vinmarshall/Radio-Shack-Time-Lapse/images/camera/camera_back_1.jpg

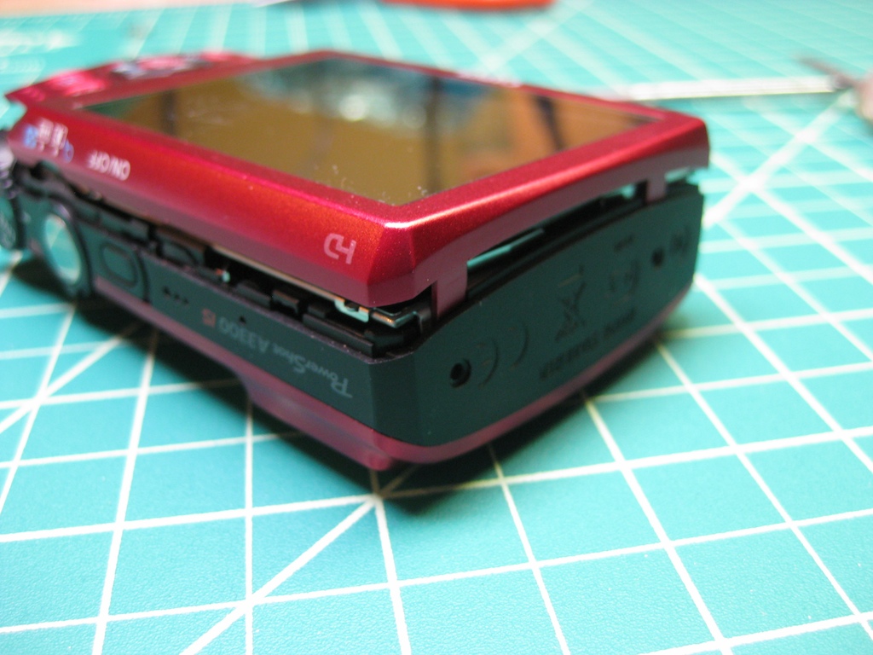
images/camera/camera_back_1.jpg
