vinmarshall/Radio-Shack-Time-Lapse/images/camera/camera_back_2.jpg

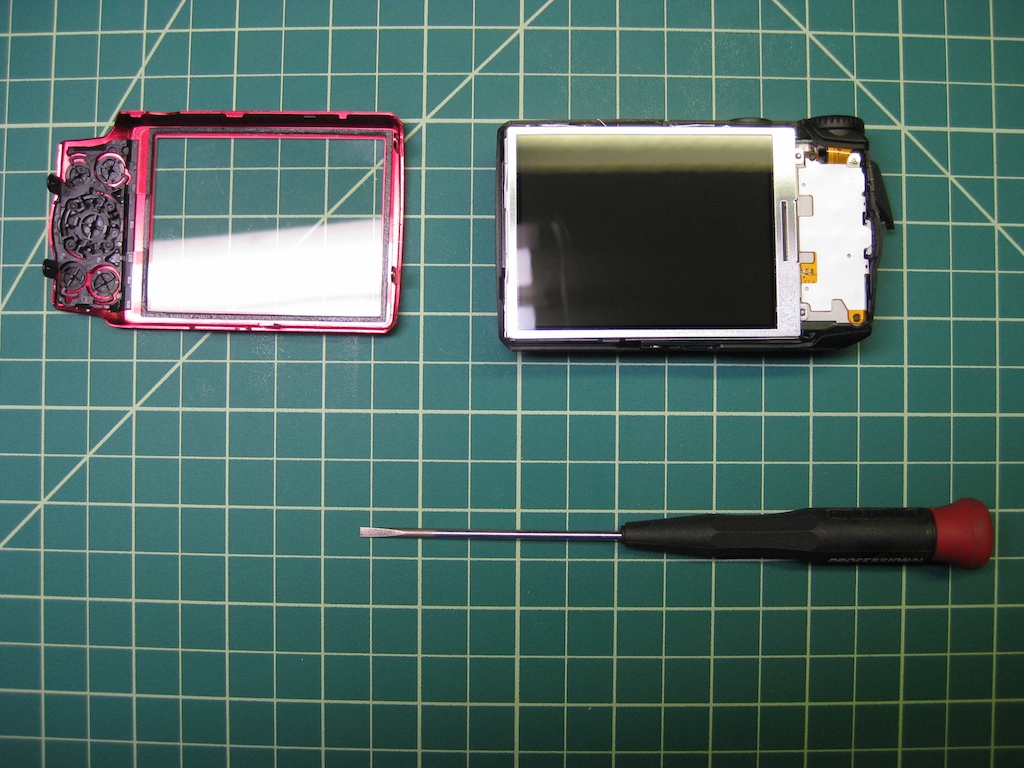
images/camera/camera_back_2.jpg
