vinmarshall/Radio-Shack-Time-Lapse/images/camera/camera_button_cover_1.jpg

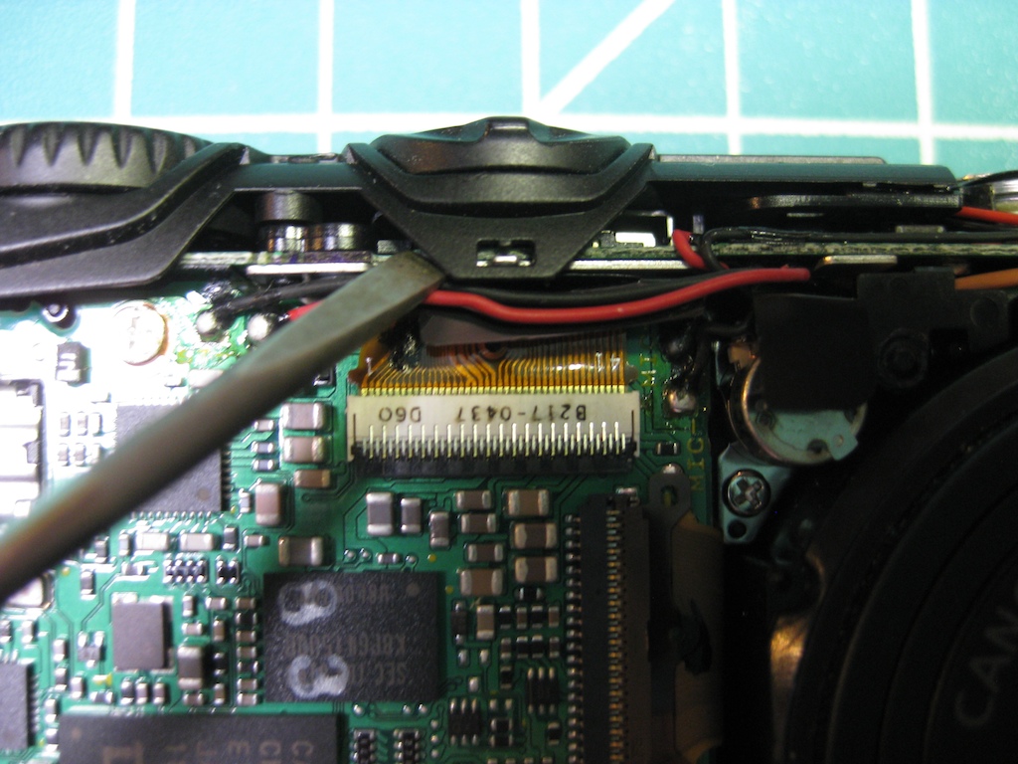
images/camera/camera_button_cover_1.jpg
