vinmarshall/Radio-Shack-Time-Lapse/images/camera/camera_button_cover_2.jpg

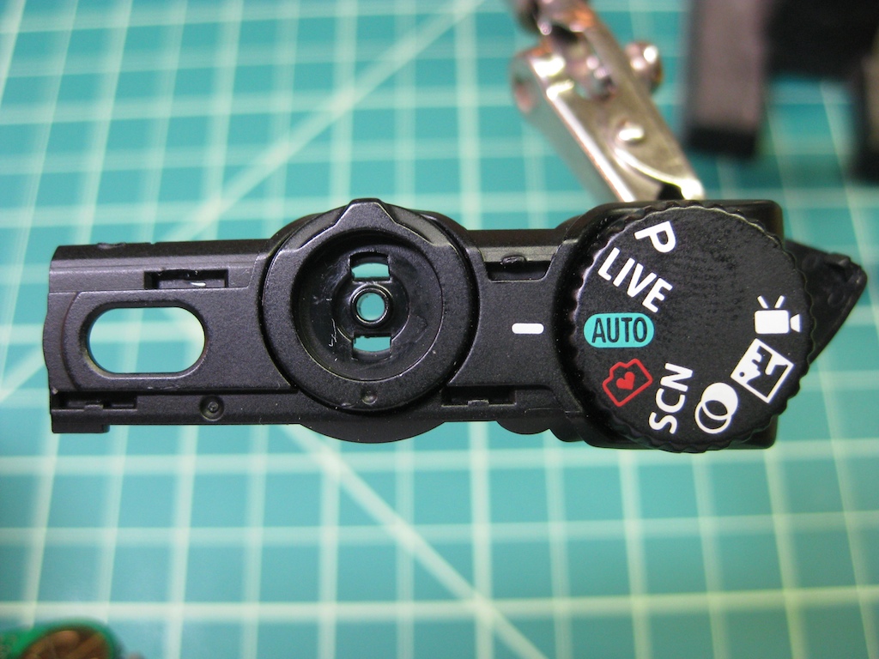
images/camera/camera_button_cover_2.jpg
