vinmarshall/Radio-Shack-Time-Lapse/images/camera/camera_button_cover_3.jpg

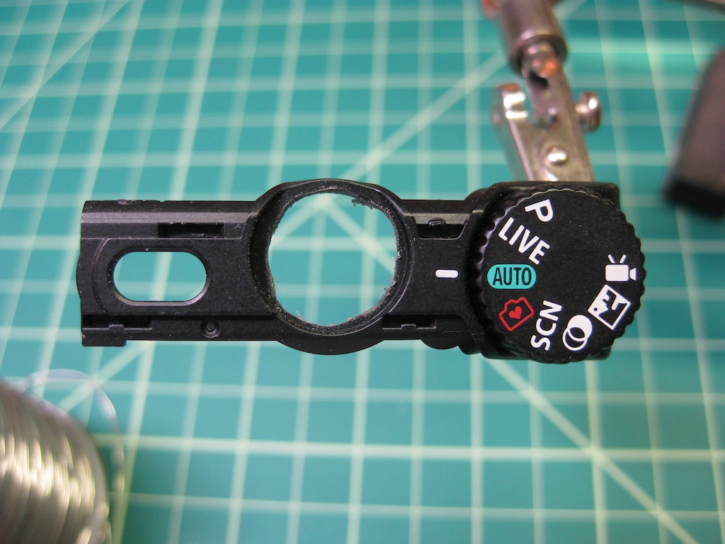
images/camera/camera_button_cover_3.jpg
