vinmarshall/Radio-Shack-Time-Lapse/images/camera/camera_front_1.jpg

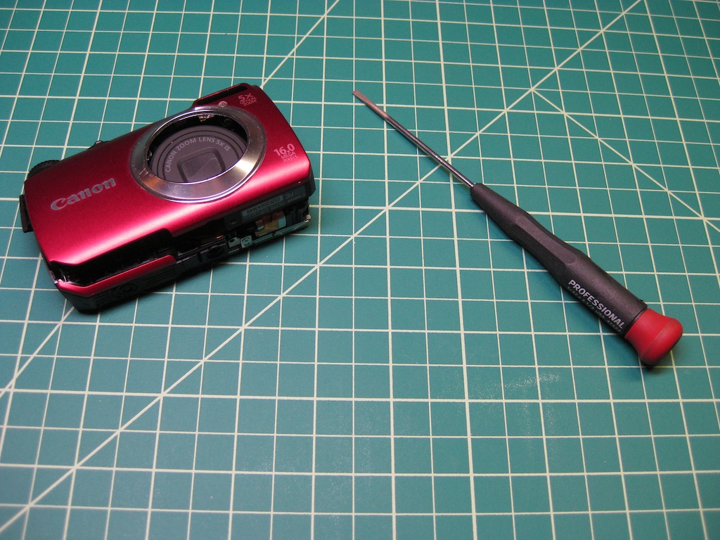
images/camera/camera_front_1.jpg
