vinmarshall/Radio-Shack-Time-Lapse/images/camera/camera_front_2.jpg

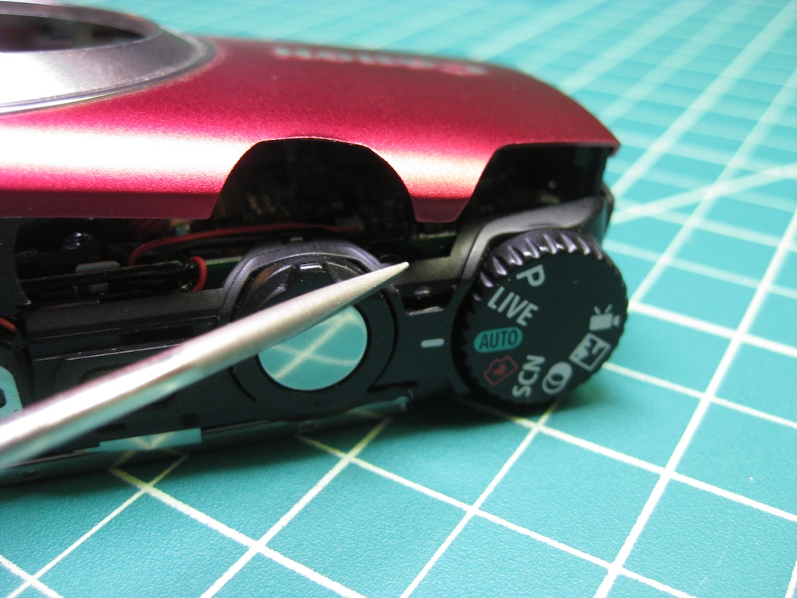
images/camera/camera_front_2.jpg
