vinmarshall/Radio-Shack-Time-Lapse/images/camera/camera_front_3.jpg

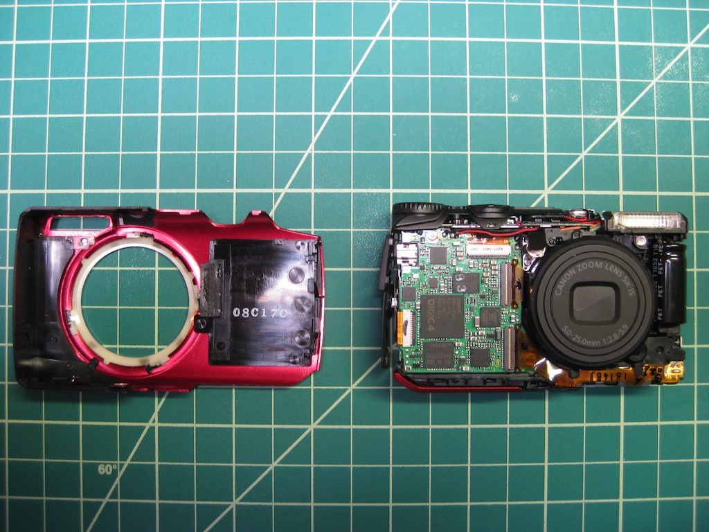
images/camera/camera_front_3.jpg
