vinmarshall/Radio-Shack-Time-Lapse/images/camera/finished.jpg

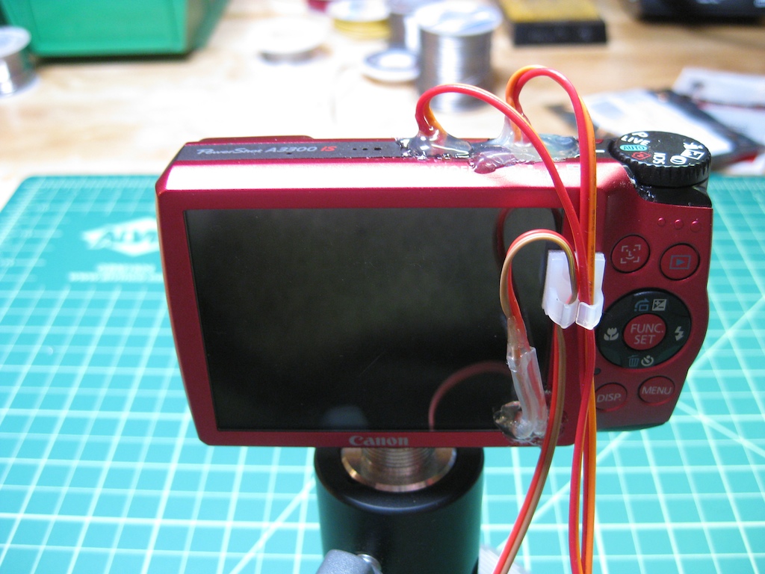
images/camera/finished.jpg
