vinmarshall/Radio-Shack-Time-Lapse/images/camera/hidden_screw.jpg

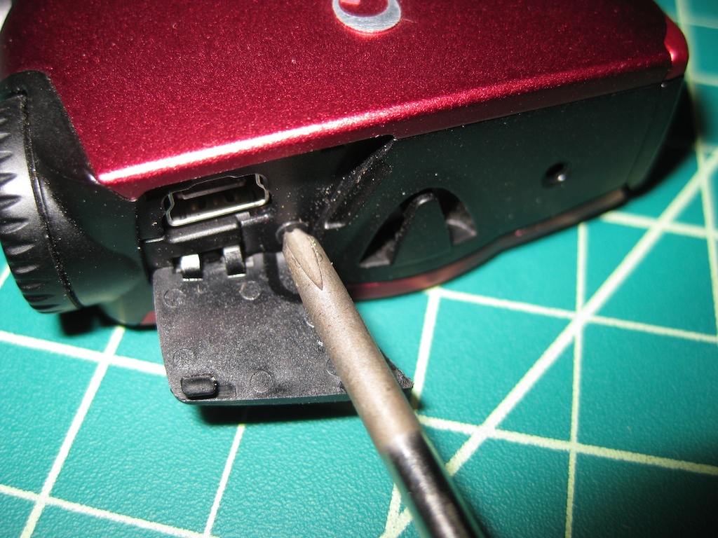
images/camera/hidden_screw.jpg
