vinmarshall/Radio-Shack-Time-Lapse/images/camera/leads_1.jpg

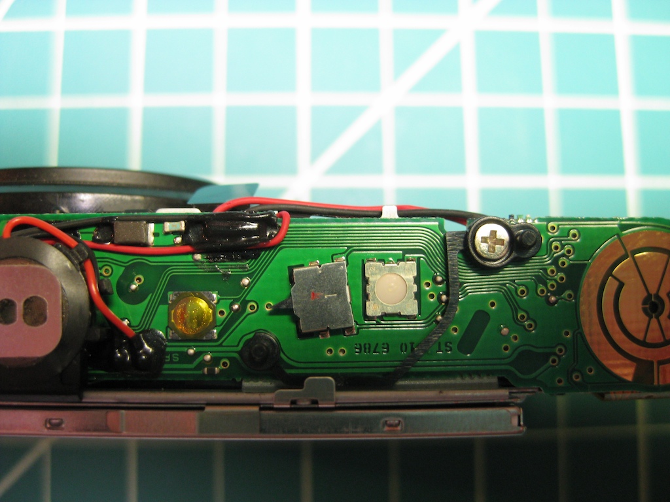
images/camera/leads_1.jpg
