vinmarshall/Radio-Shack-Time-Lapse/images/camera/leads_2.jpg

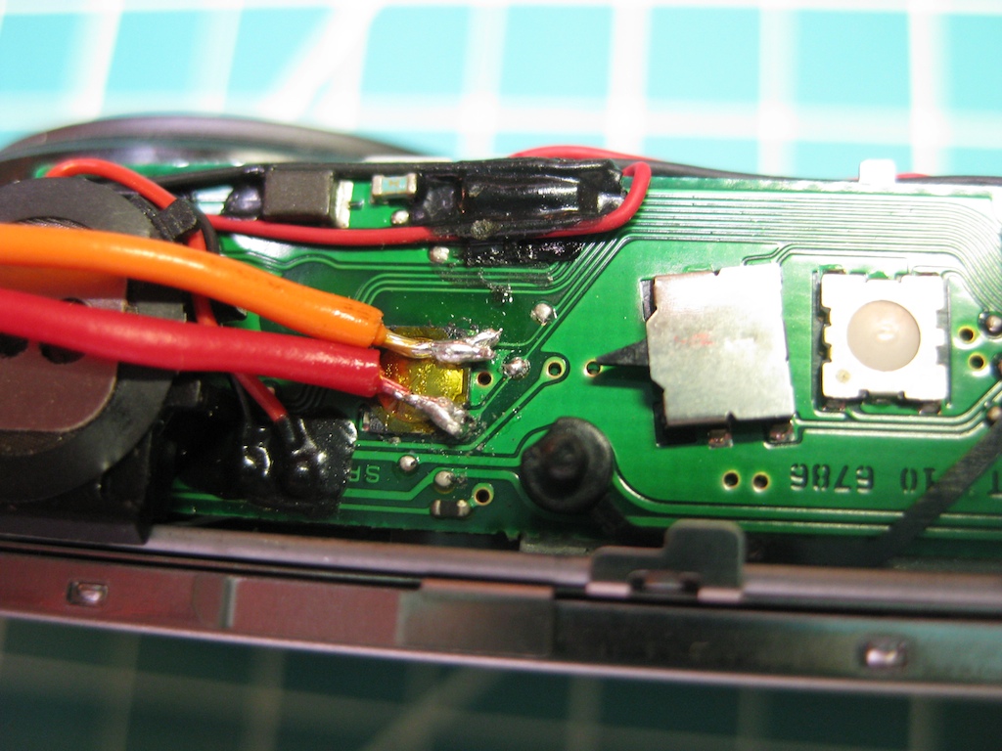
images/camera/leads_2.jpg
