vinmarshall/Radio-Shack-Time-Lapse/images/camera/leads_3.jpg

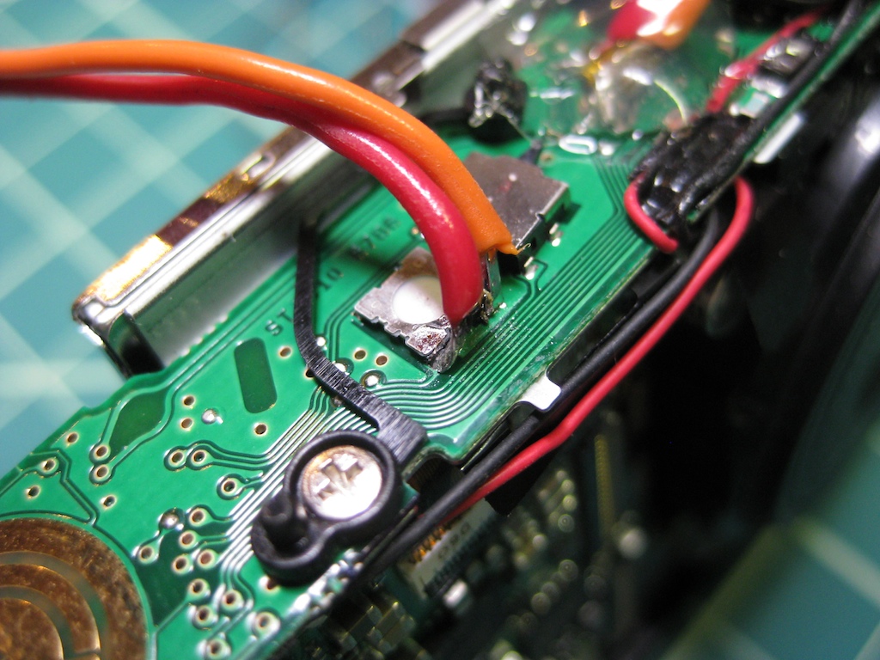
images/camera/leads_3.jpg
