vinmarshall/Radio-Shack-Time-Lapse/images/camera/leads_4.jpg

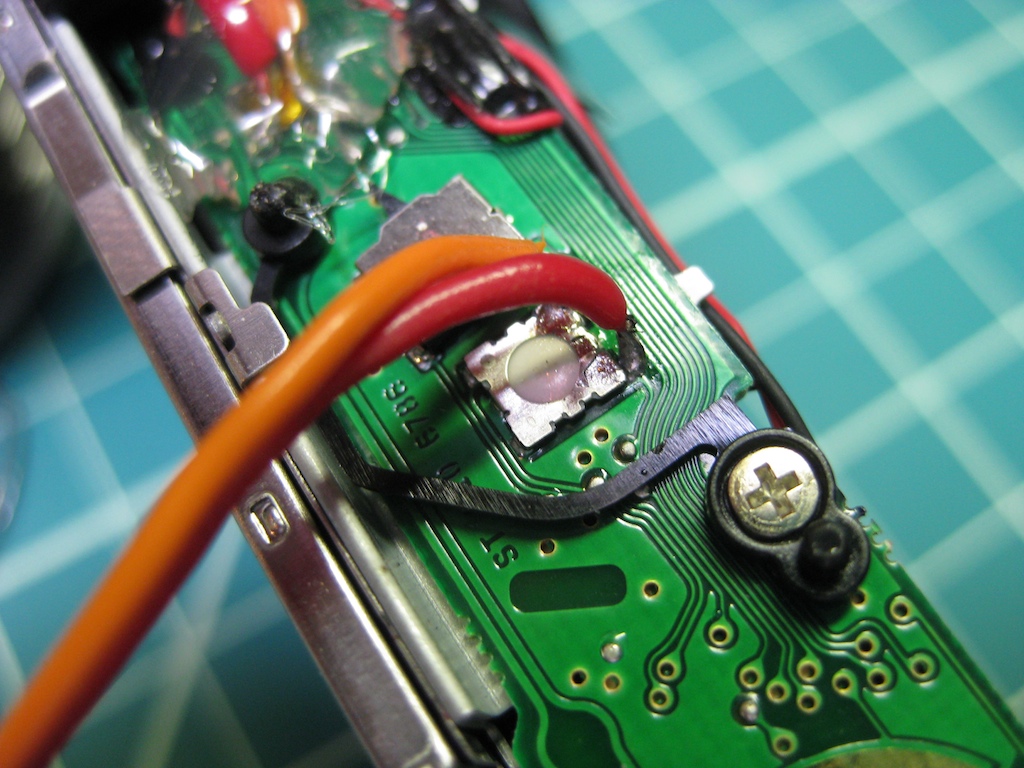
images/camera/leads_4.jpg
