vinmarshall/Radio-Shack-Time-Lapse/images/camera/leads_5.jpg

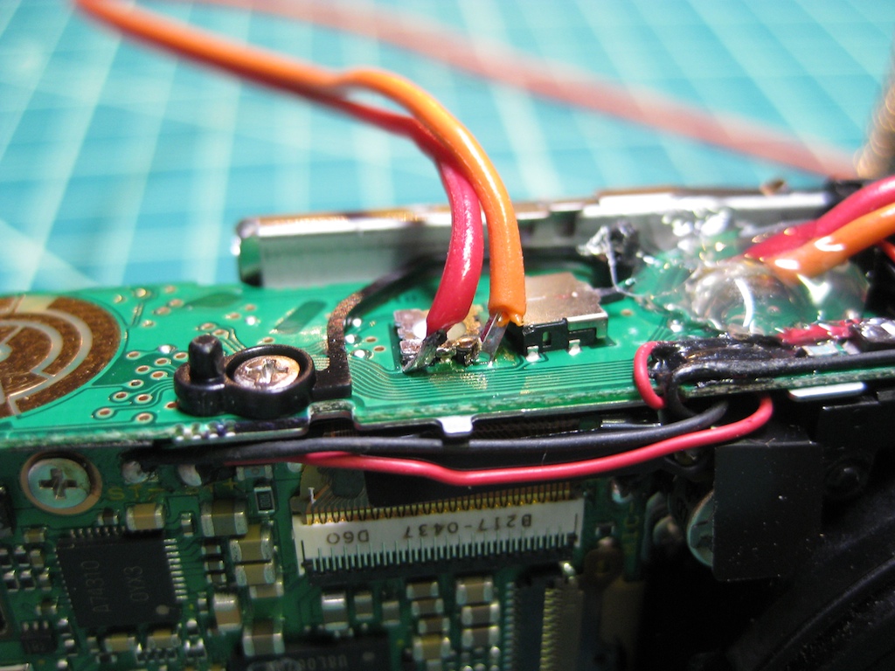
images/camera/leads_5.jpg
