vinmarshall/Radio-Shack-Time-Lapse/images/camera/leads_6.jpg

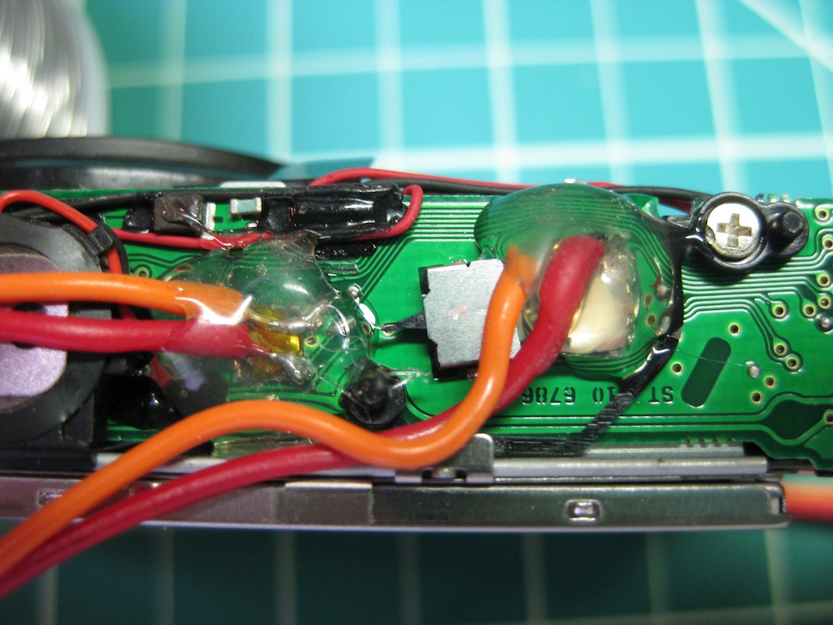
images/camera/leads_6.jpg
