vinmarshall/Radio-Shack-Time-Lapse/images/camera/leads_7.jpg

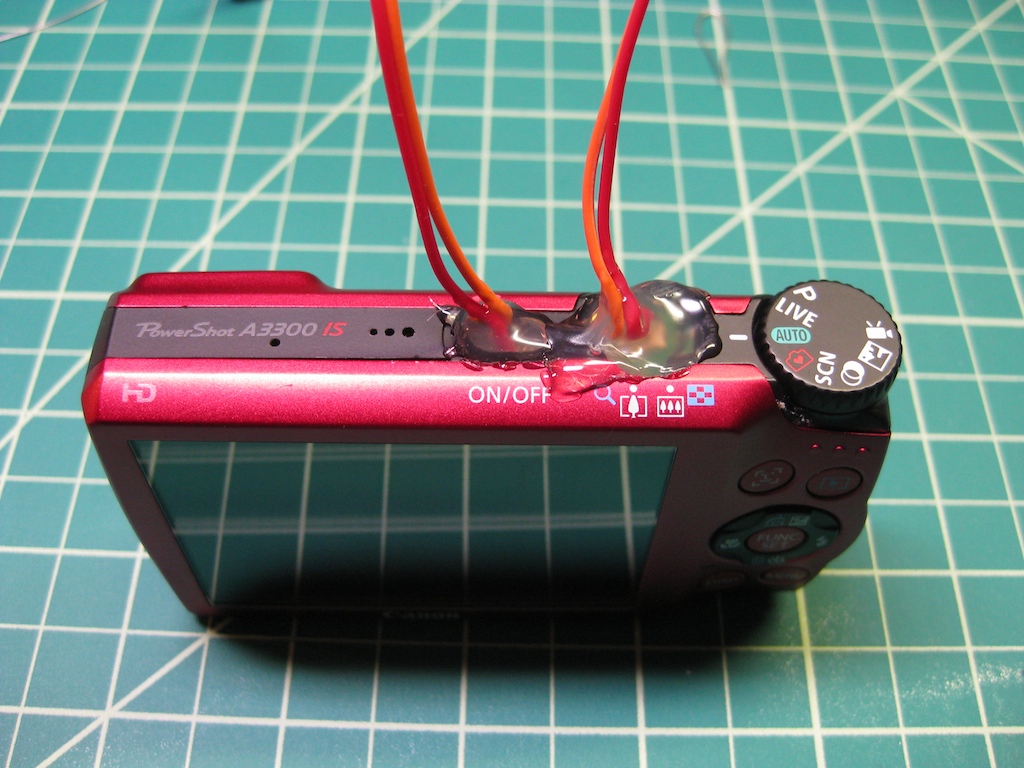
images/camera/leads_7.jpg
