vinmarshall/Radio-Shack-Time-Lapse/images/camera/leads_8.jpg

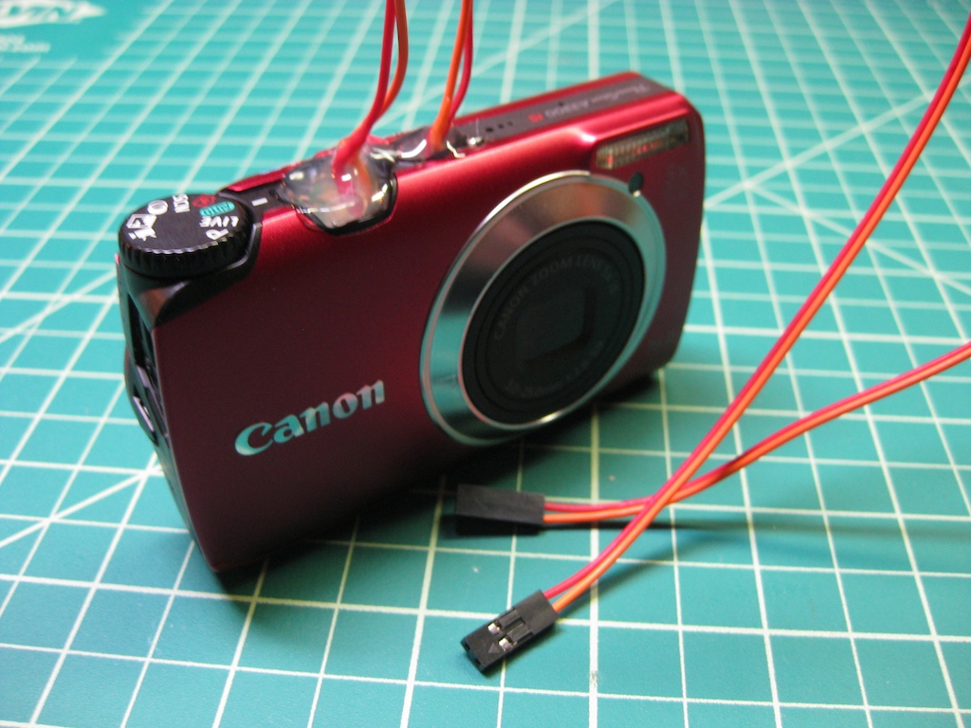
images/camera/leads_8.jpg
