vinmarshall/Radio-Shack-Time-Lapse/images/camera/photoresistor_1.jpg

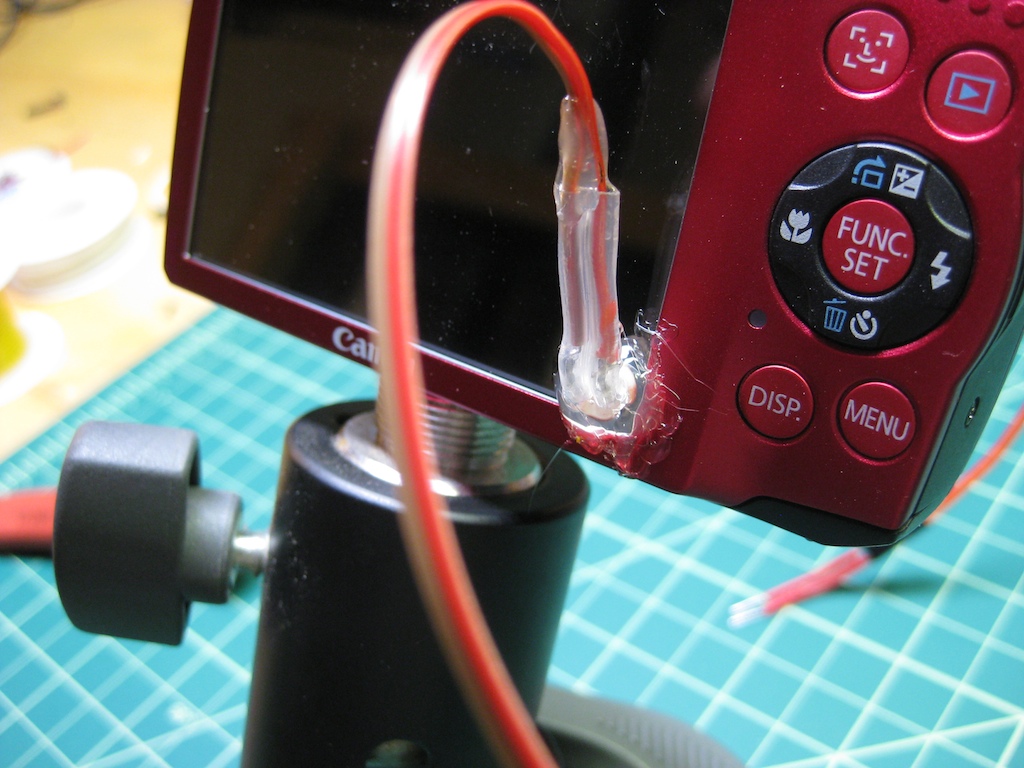
images/camera/photoresistor_1.jpg
