vinmarshall/Radio-Shack-Time-Lapse/images/camera/photoresistor_2.jpg

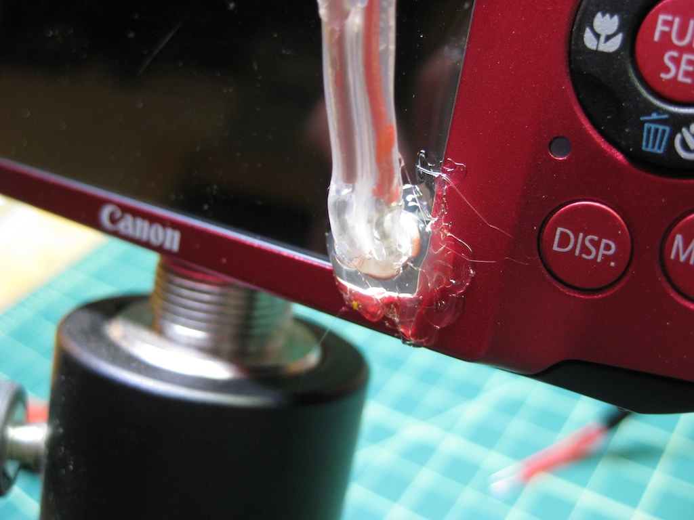
images/camera/photoresistor_2.jpg
