vinmarshall/Radio-Shack-Time-Lapse/images/camera/the_buttons.jpg

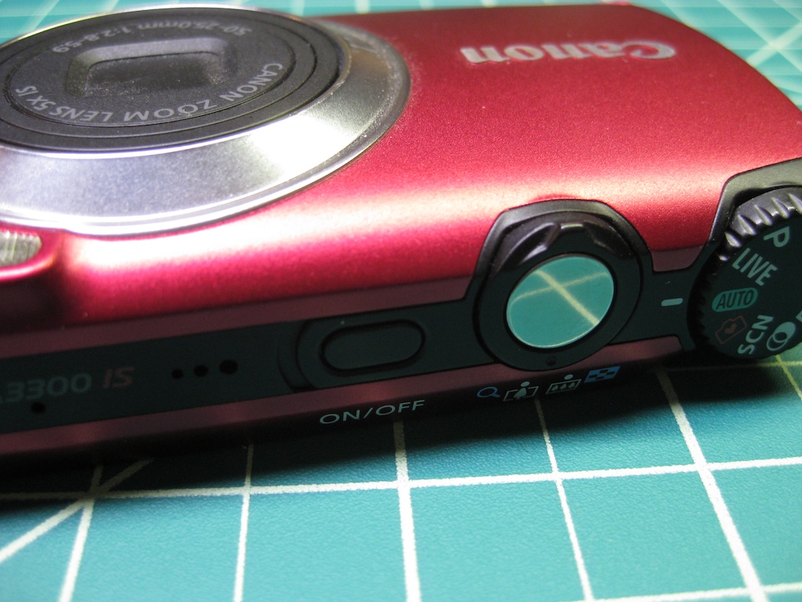
images/camera/the_buttons.jpg
