vinmarshall/Radio-Shack-Time-Lapse/images/panel/jumper.jpg

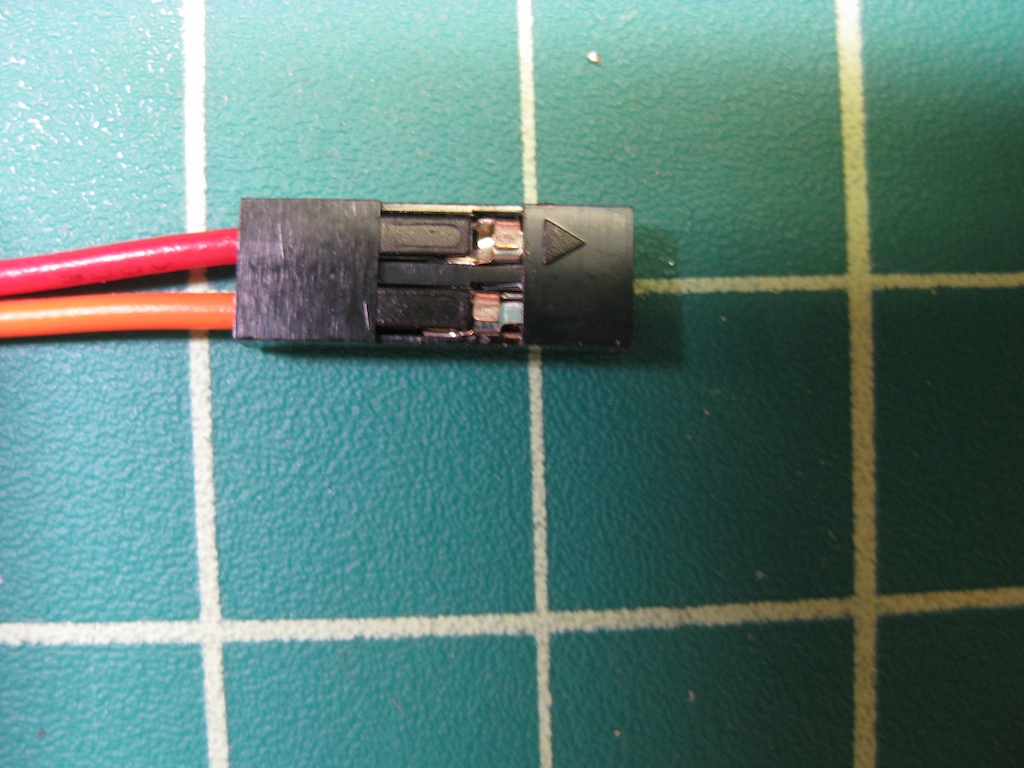
images/panel/jumper.jpg
