vinmarshall/Radio-Shack-Time-Lapse/images/panel/lamp_1.jpg

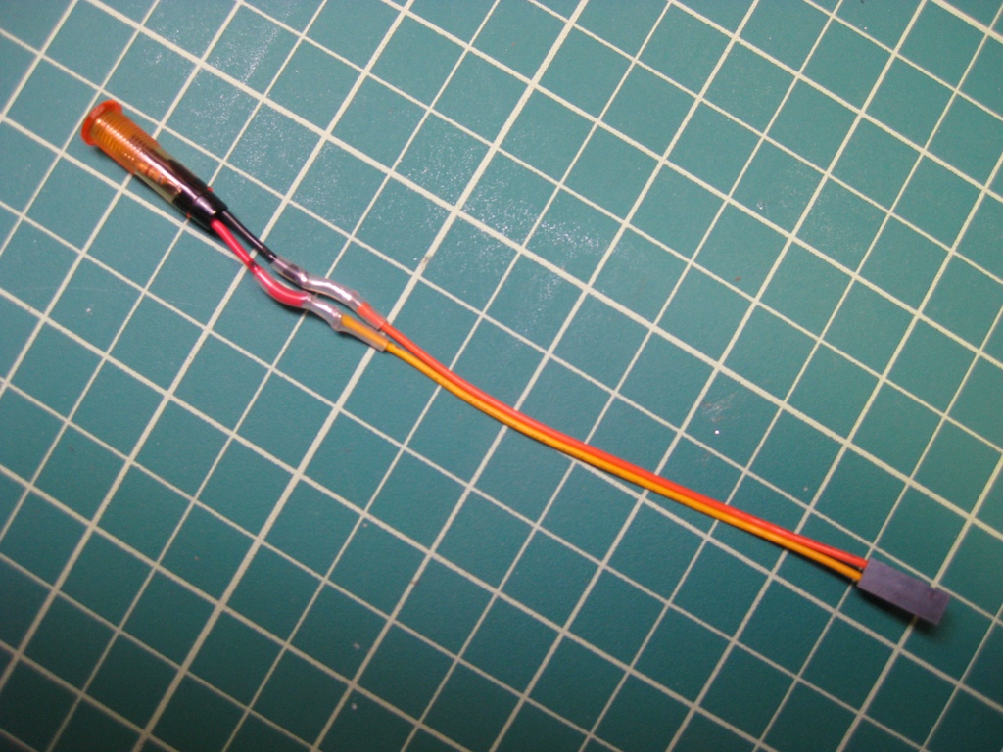
images/panel/lamp_1.jpg
