vinmarshall/Radio-Shack-Time-Lapse/images/panel/lamp_2.jpg

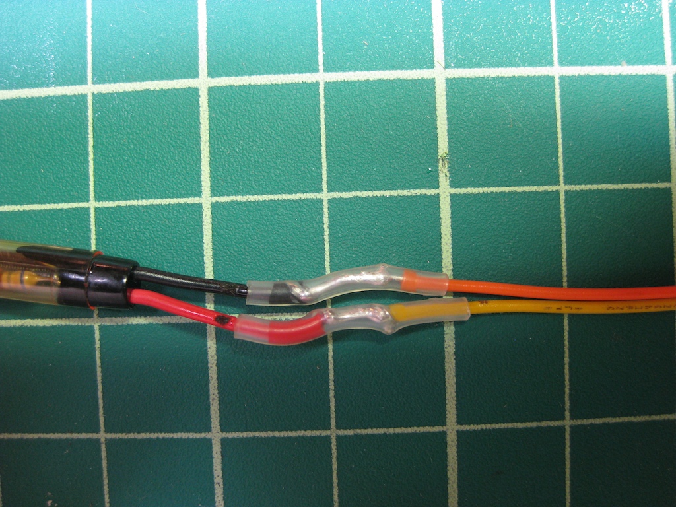
images/panel/lamp_2.jpg
