vinmarshall/Radio-Shack-Time-Lapse/images/panel/lamp_3.jpg

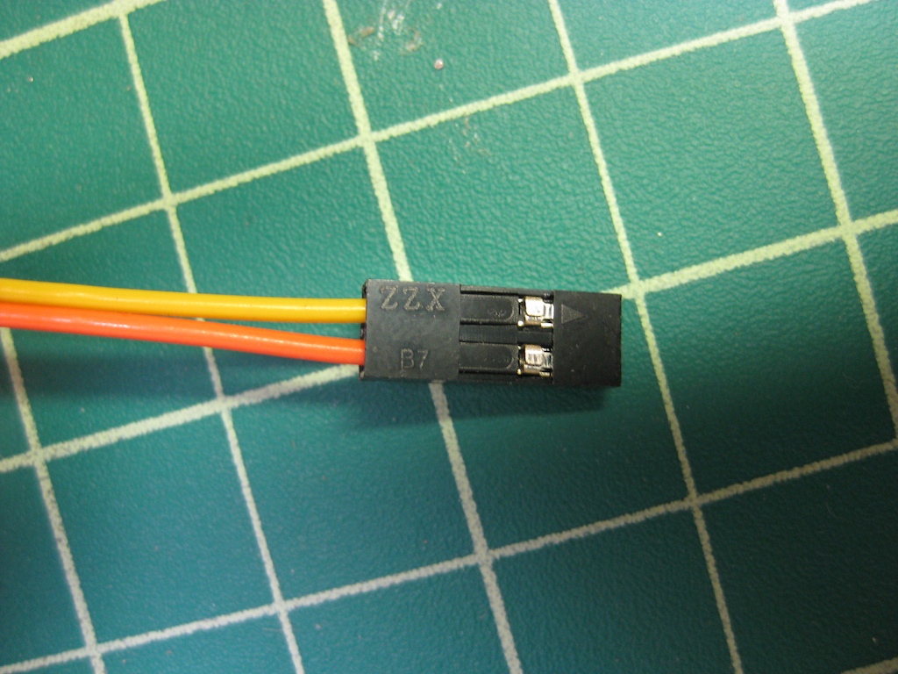
images/panel/lamp_3.jpg
