vinmarshall/Radio-Shack-Time-Lapse/images/panel/panel_back.jpg

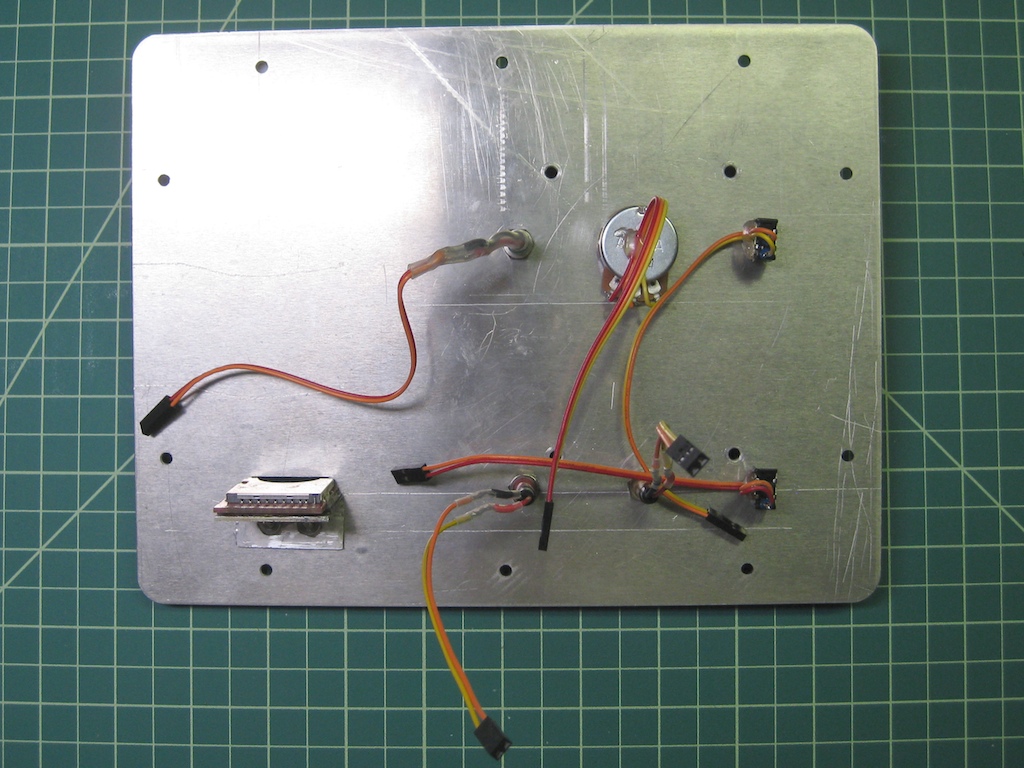
images/panel/panel_back.jpg
