vinmarshall/Radio-Shack-Time-Lapse/images/panel/panel_front.jpg

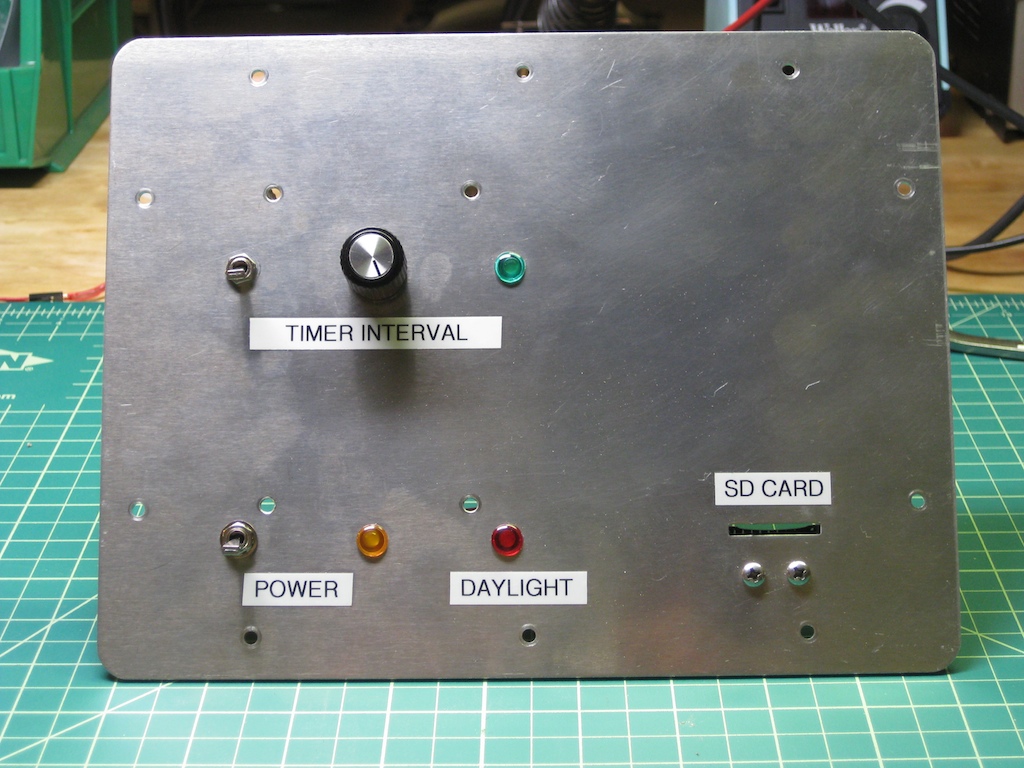
images/panel/panel_front.jpg
