vinmarshall/Radio-Shack-Time-Lapse/images/panel/pins.jpg

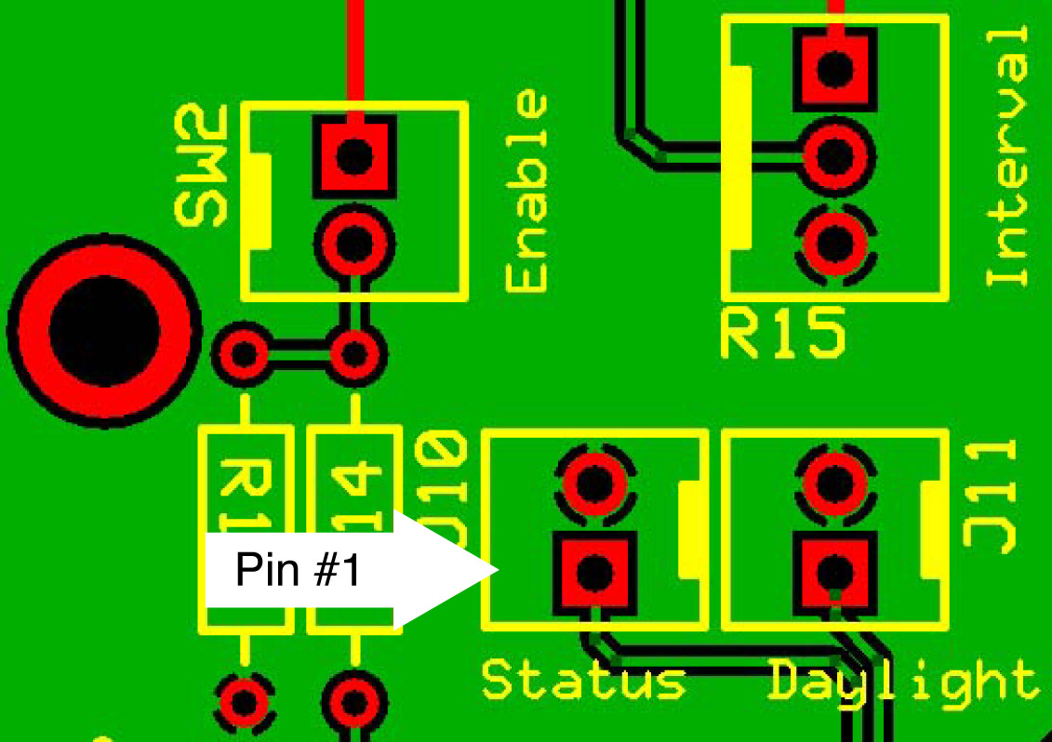
images/panel/pins.jpg
