vinmarshall/Radio-Shack-Time-Lapse/images/panel/pot_1.jpg

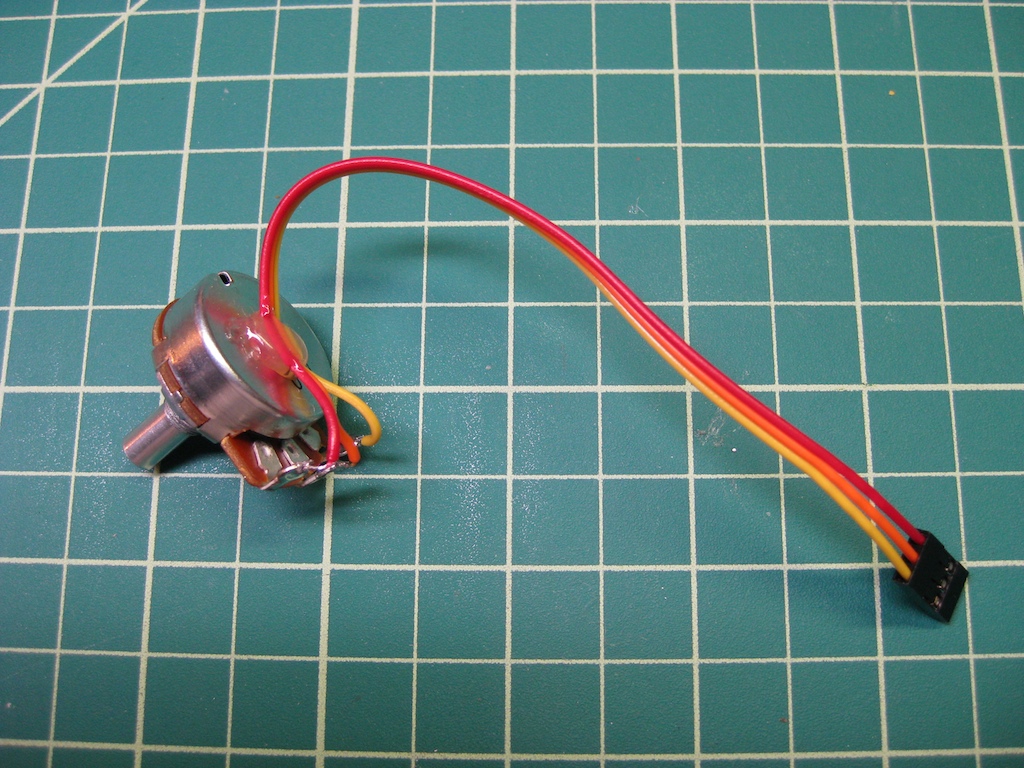
images/panel/pot_1.jpg
