vinmarshall/Radio-Shack-Time-Lapse/images/panel/pot_2.jpg

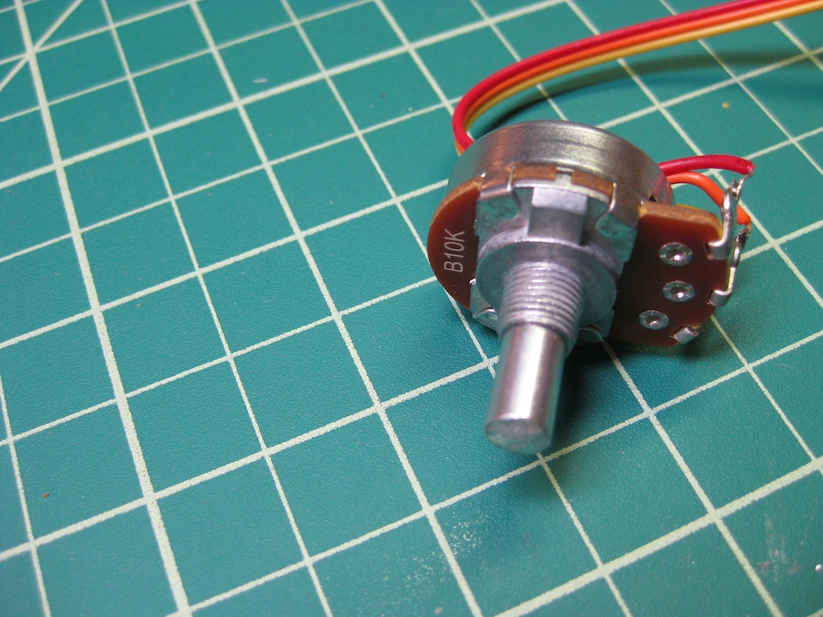
images/panel/pot_2.jpg
