vinmarshall/Radio-Shack-Time-Lapse/images/panel/pot_3.jpg

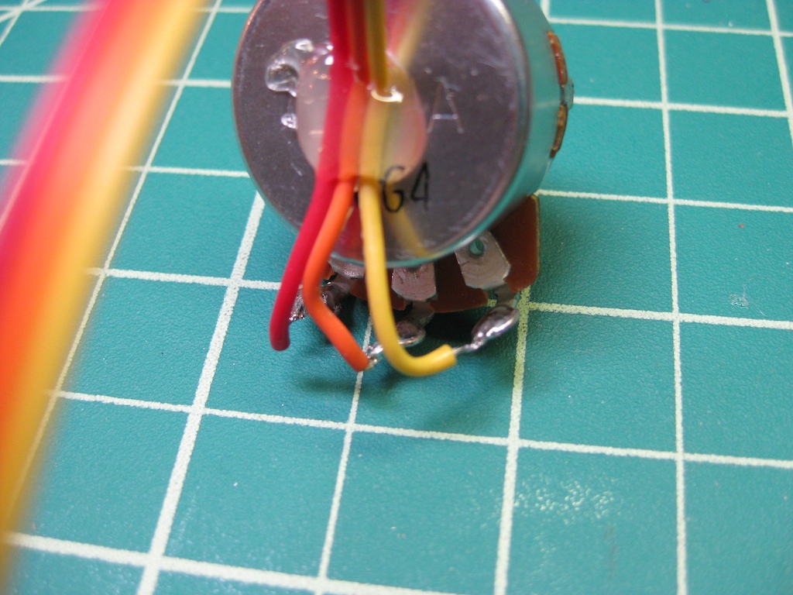
images/panel/pot_3.jpg
