vinmarshall/Radio-Shack-Time-Lapse/images/panel/pot_4.jpg

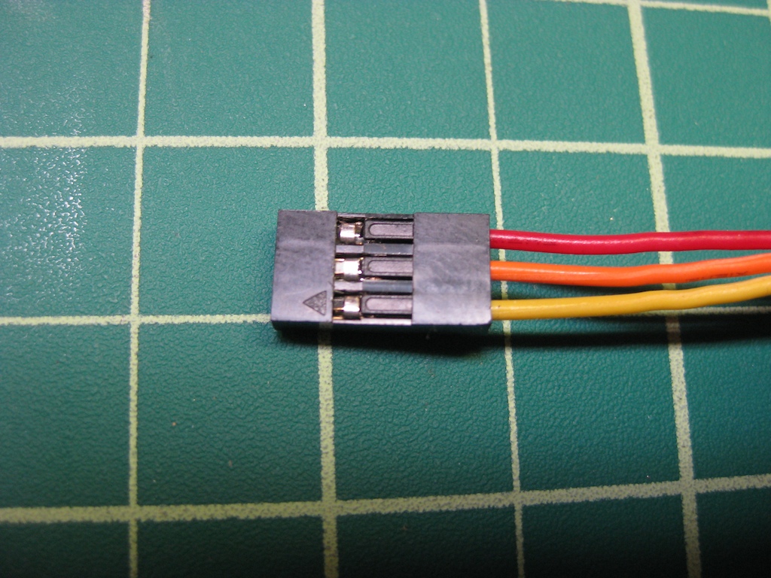
images/panel/pot_4.jpg
