vinmarshall/Radio-Shack-Time-Lapse/images/panel/toggle_switch_1.jpg

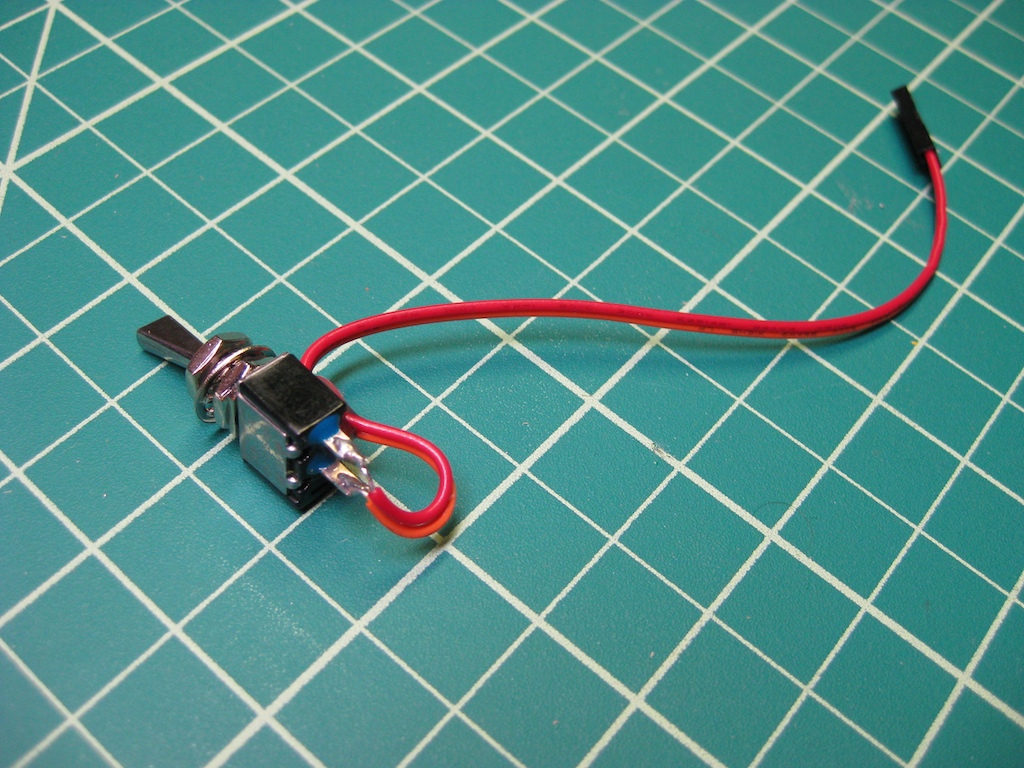
images/panel/toggle_switch_1.jpg
