vinmarshall/Radio-Shack-Time-Lapse/images/pelican/battery_1.jpg

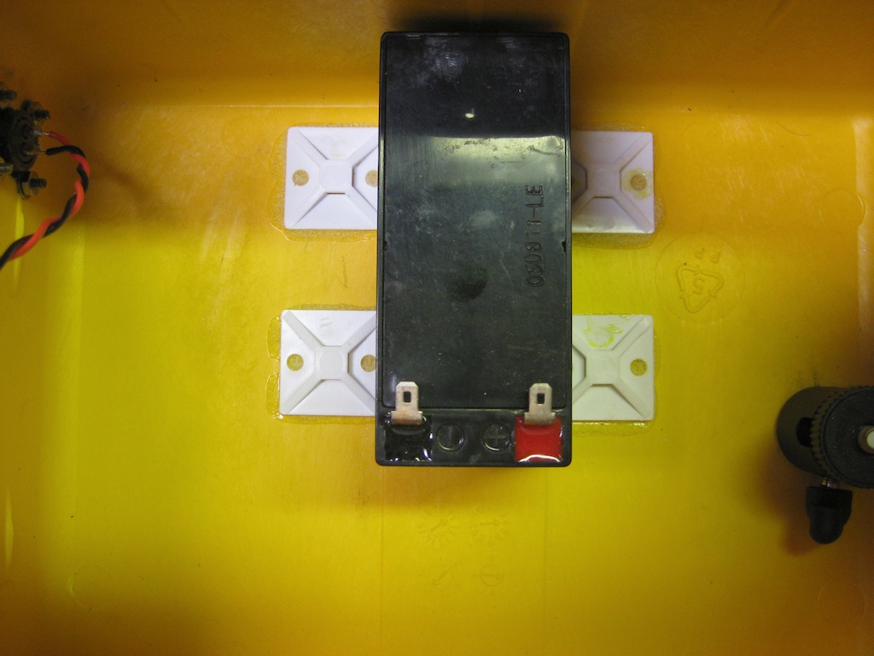
images/pelican/battery_1.jpg
