vinmarshall/Radio-Shack-Time-Lapse/images/pelican/battery_2.jpg

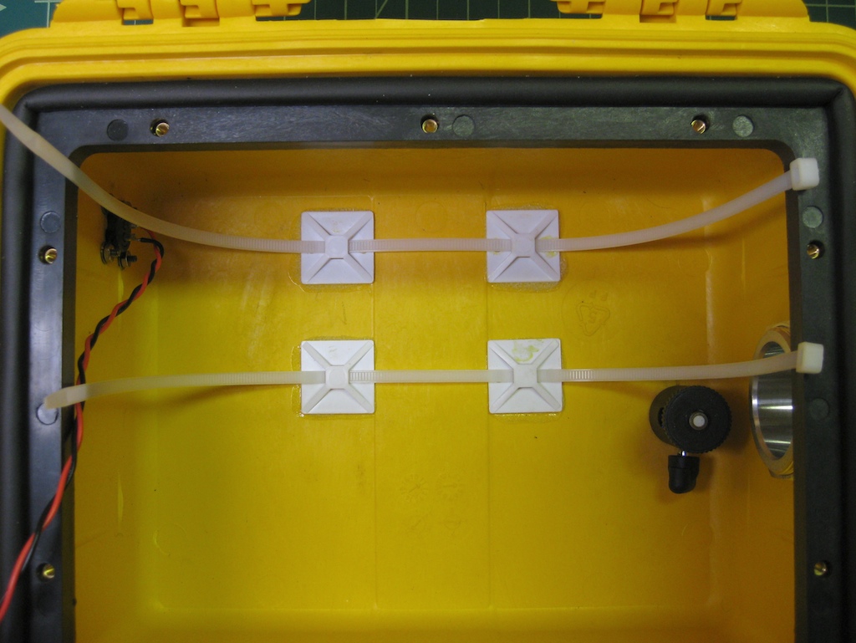
images/pelican/battery_2.jpg
