vinmarshall/Radio-Shack-Time-Lapse/images/pelican/battery_3.jpg

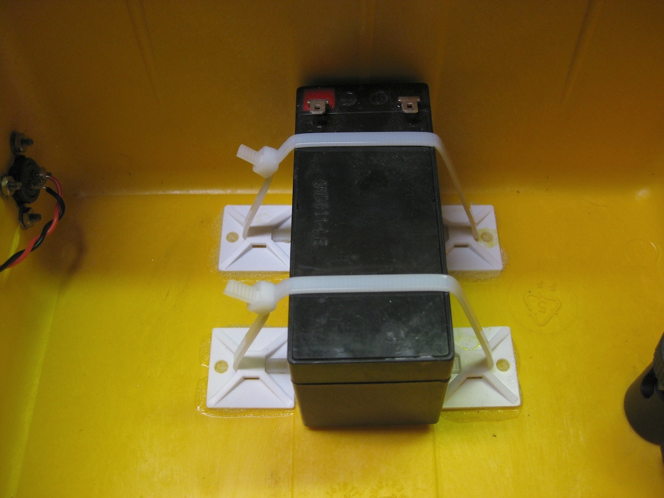
images/pelican/battery_3.jpg
