vinmarshall/Radio-Shack-Time-Lapse/images/pelican/camera_mount_1.jpg

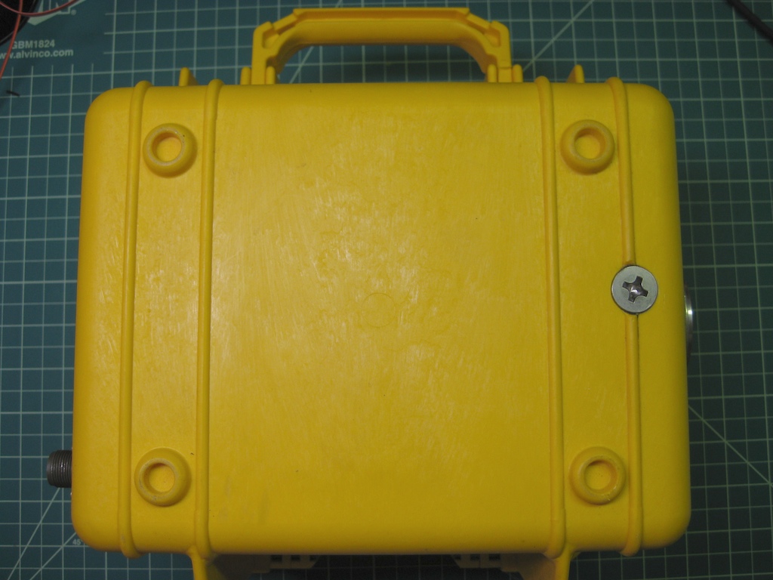
images/pelican/camera_mount_1.jpg
