vinmarshall/Radio-Shack-Time-Lapse/images/pelican/camera_mount_2.jpg

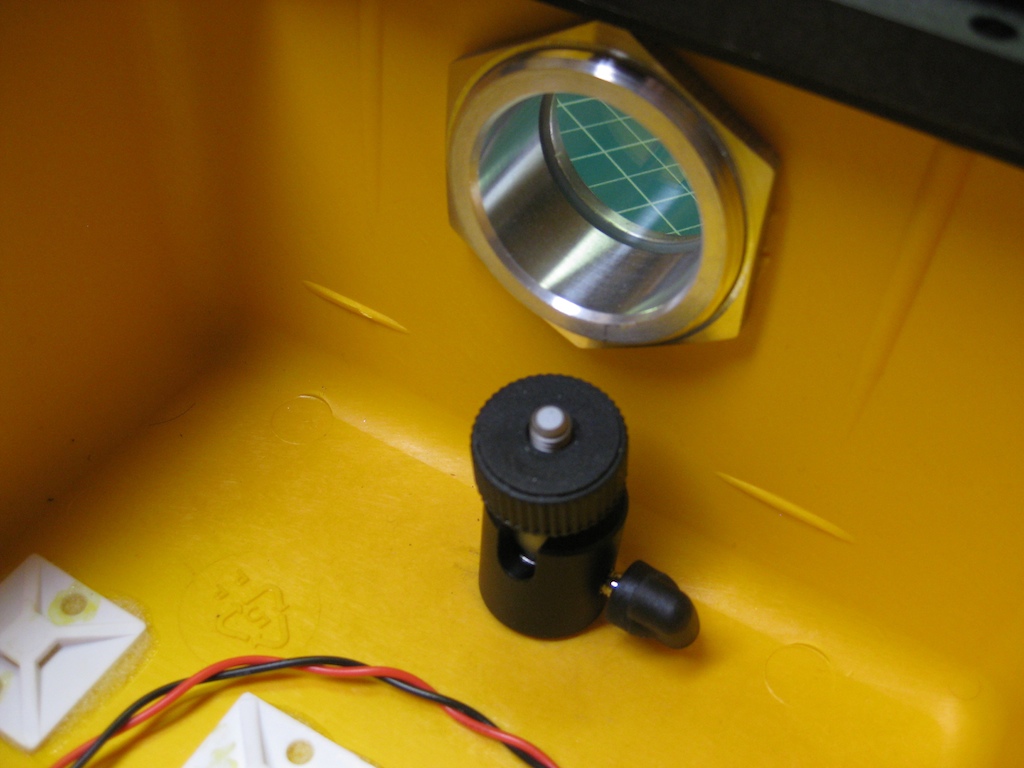
images/pelican/camera_mount_2.jpg
