vinmarshall/Radio-Shack-Time-Lapse/images/pelican/camera_mount_3.jpg

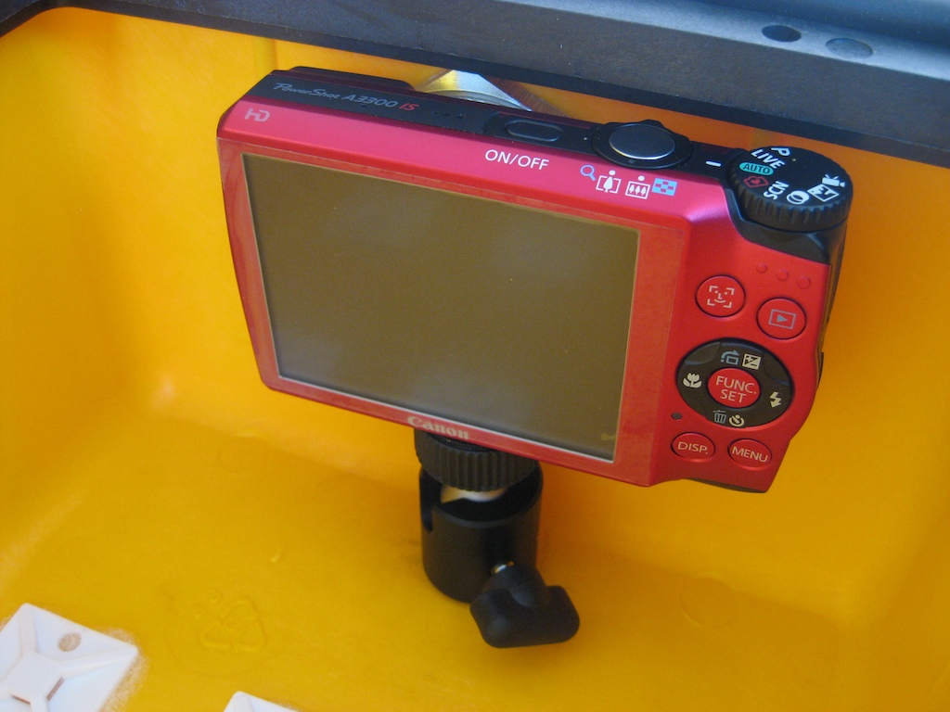
images/pelican/camera_mount_3.jpg
