vinmarshall/Radio-Shack-Time-Lapse/images/pelican/layout.jpg

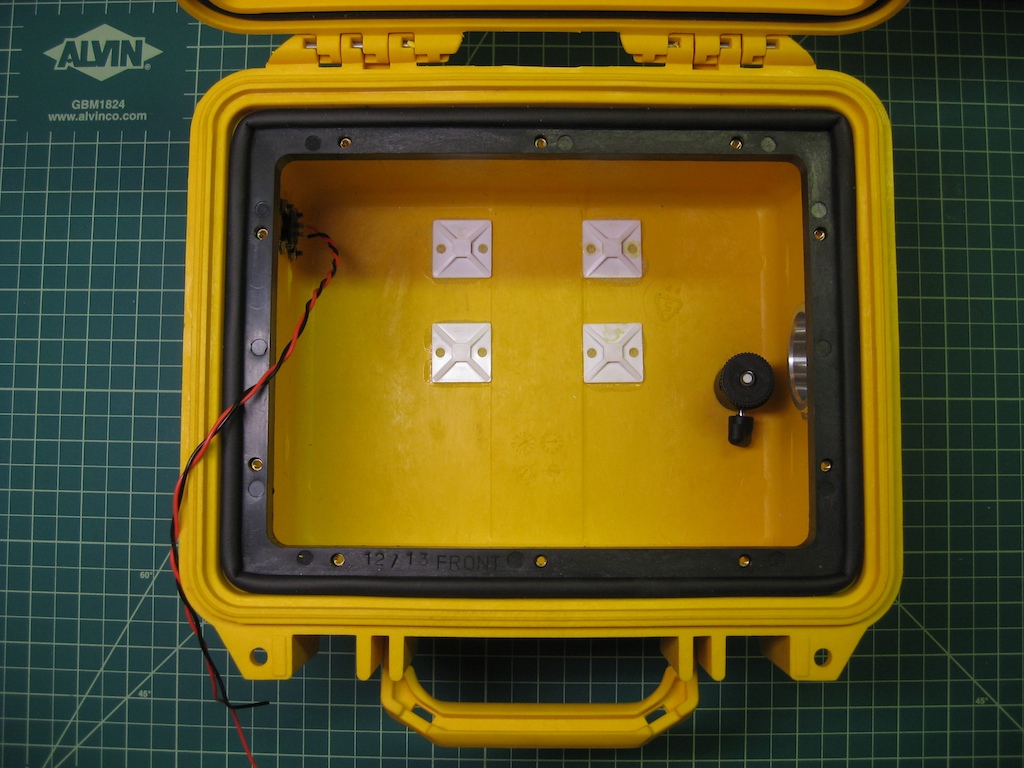
images/pelican/layout.jpg
