vinmarshall/Radio-Shack-Time-Lapse/images/pelican/portal  001.jpg

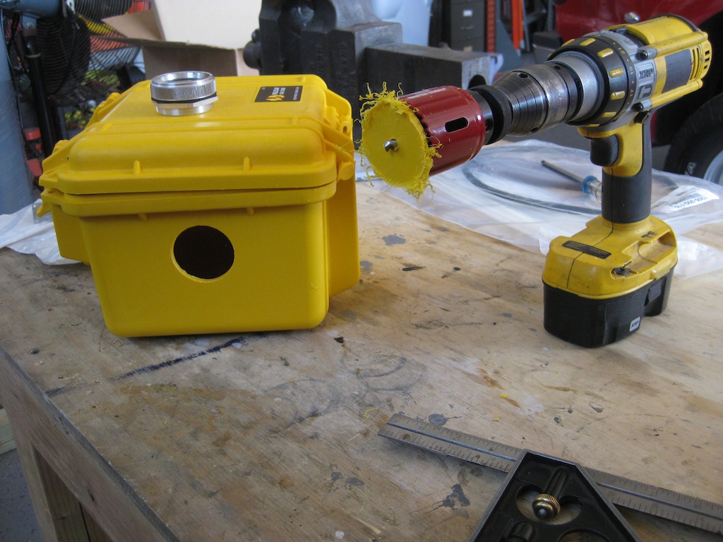
images/pelican/portal 001.jpg
