vinmarshall/Radio-Shack-Time-Lapse/images/pelican/portal  002.jpg

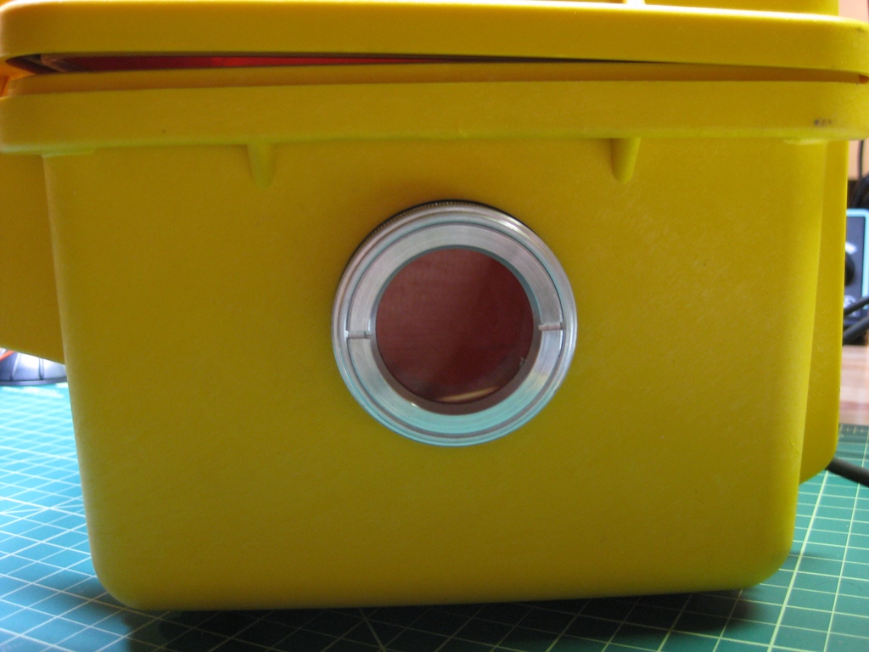
images/pelican/portal 002.jpg
