vinmarshall/Radio-Shack-Time-Lapse/images/pelican/solar_port_1.jpg

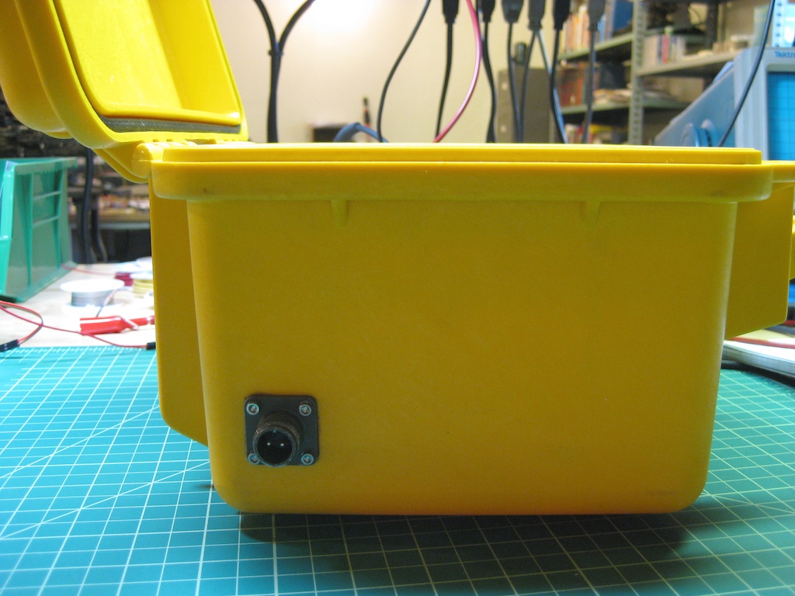
images/pelican/solar_port_1.jpg
