vinmarshall/Radio-Shack-Time-Lapse/images/pelican/solar_port_2.jpg

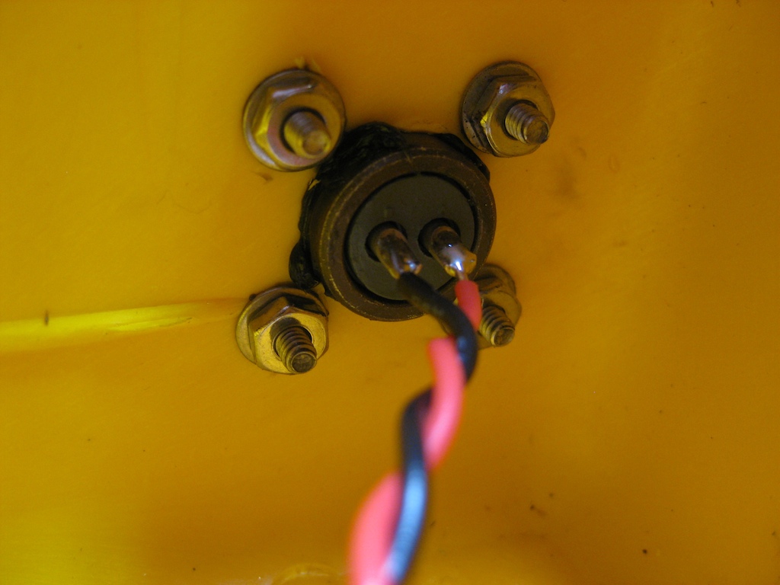
images/pelican/solar_port_2.jpg
