vinmarshall/Radio-Shack-Time-Lapse/images/prototype/prototype  003.jpg

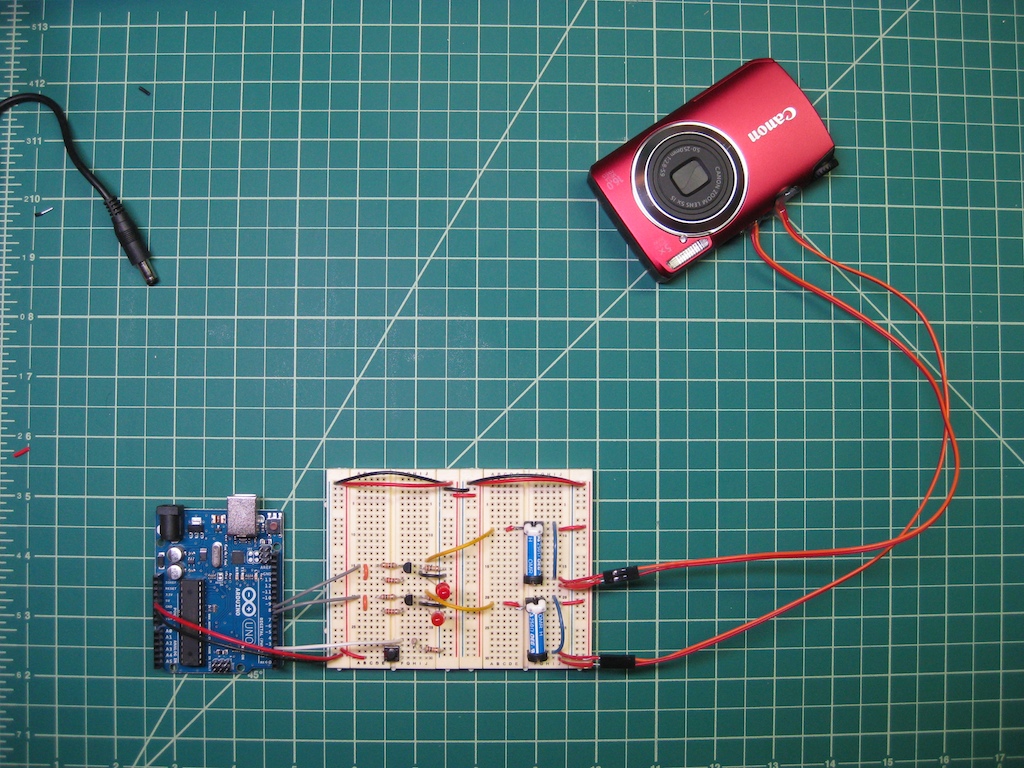
images/prototype/prototype 003.jpg
