vinmarshall/Radio-Shack-Time-Lapse/images/prototype/prototype  004.jpg

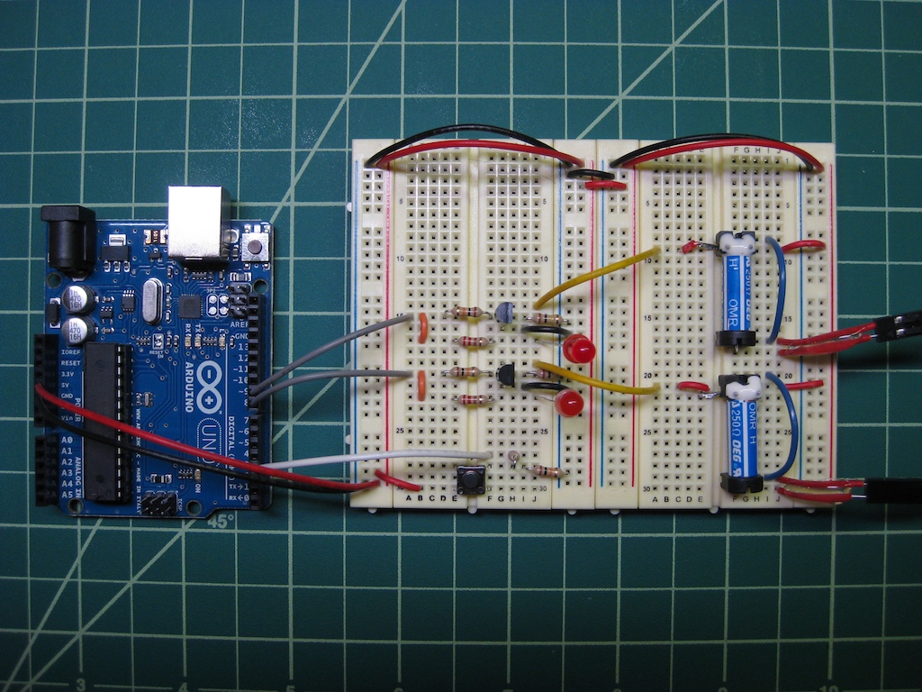
images/prototype/prototype 004.jpg
