vinmarshall/Radio-Shack-Time-Lapse/images/prototype/prototype  005.jpg

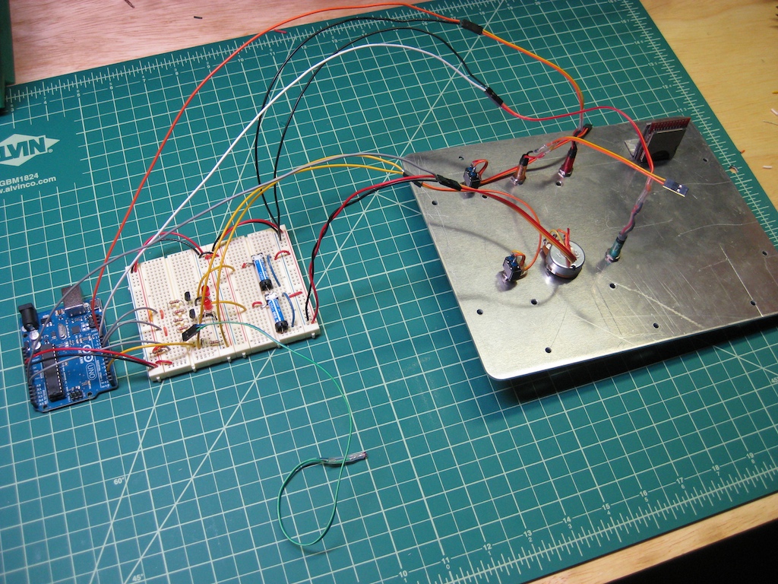
images/prototype/prototype 005.jpg
