vinmarshall/Radio-Shack-Time-Lapse/images/prototype/prototype  006.jpg

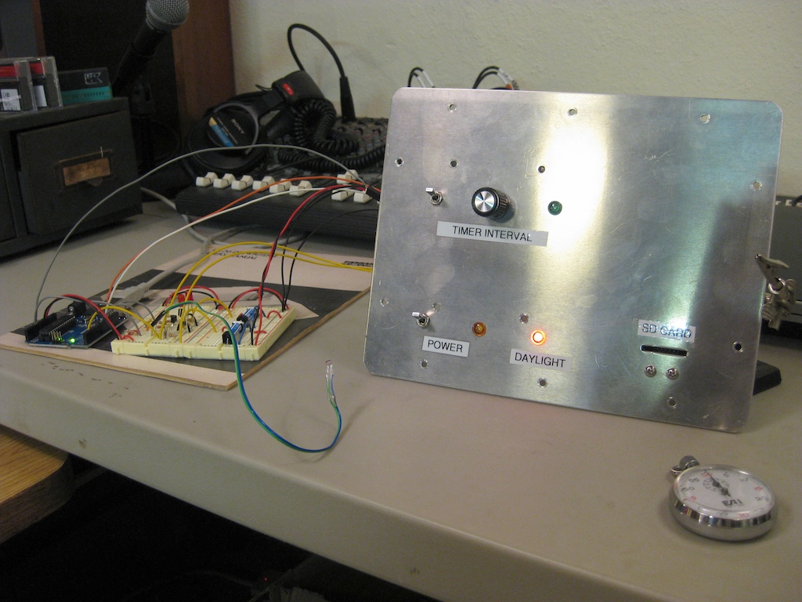
images/prototype/prototype 006.jpg
