vinmarshall/Radio-Shack-Time-Lapse/images/prototype/prototype  007.jpg

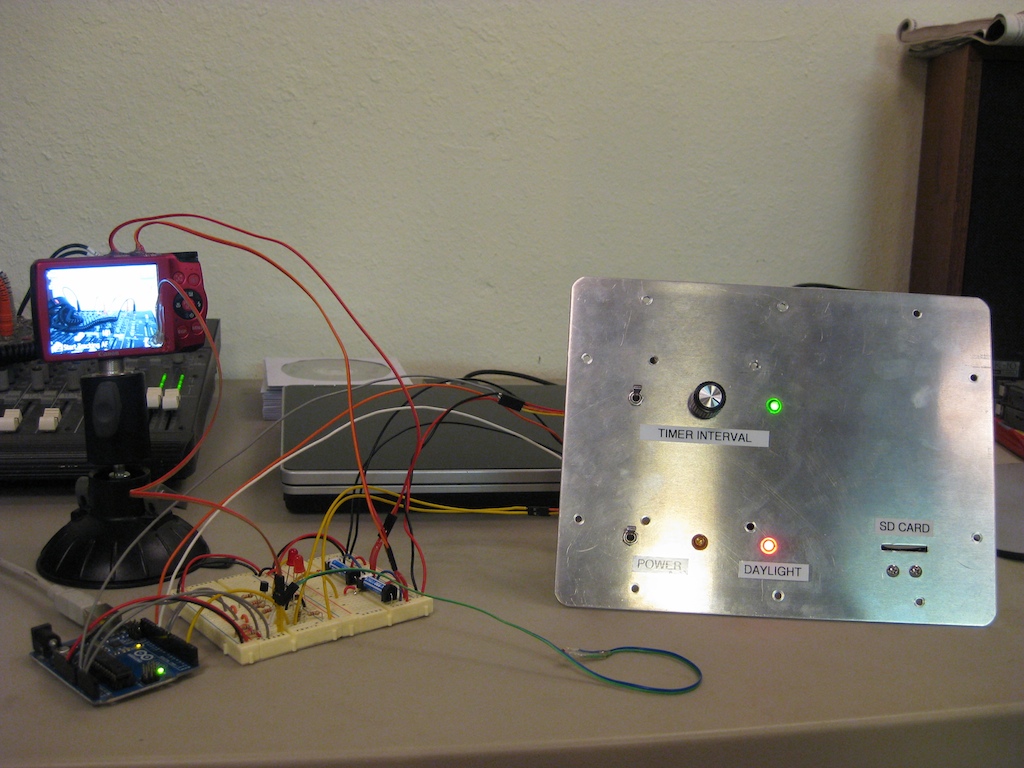
images/prototype/prototype 007.jpg
