vinmarshall/Radio-Shack-Time-Lapse/images/prototype/prototype  008.jpg

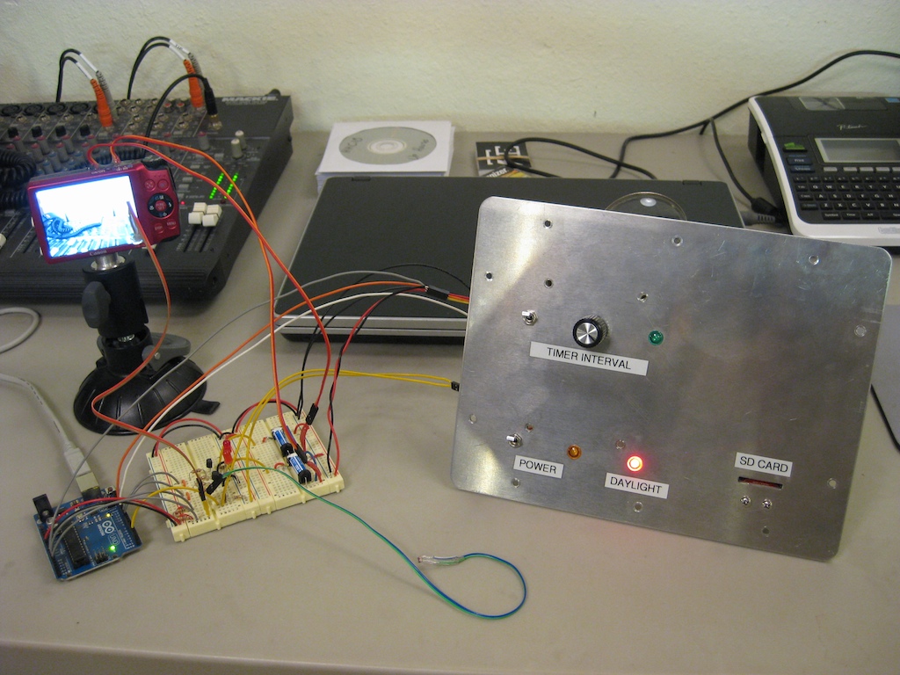
images/prototype/prototype 008.jpg
