vinmarshall/Radio-Shack-Time-Lapse/PCB/pcb_components.bmp

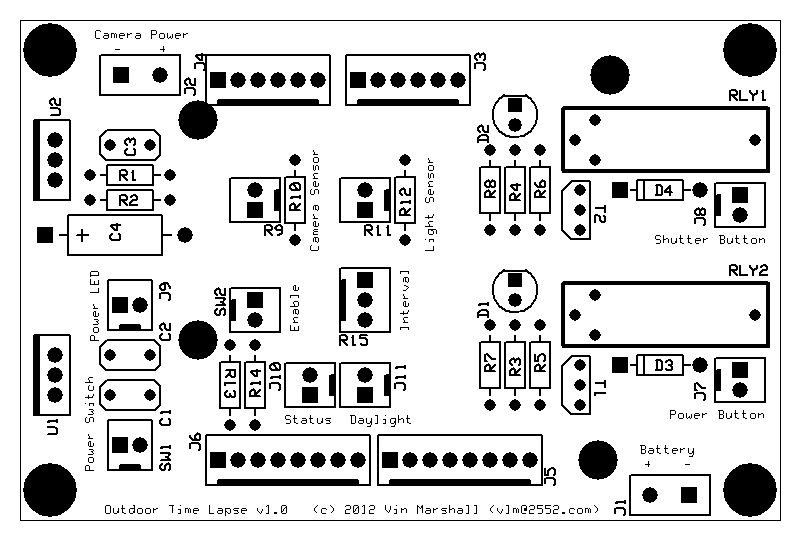
PCB/pcb_components.bmp
