vinmarshall/Radio-Shack-Time-Lapse/images/wiring/battery_2.jpg

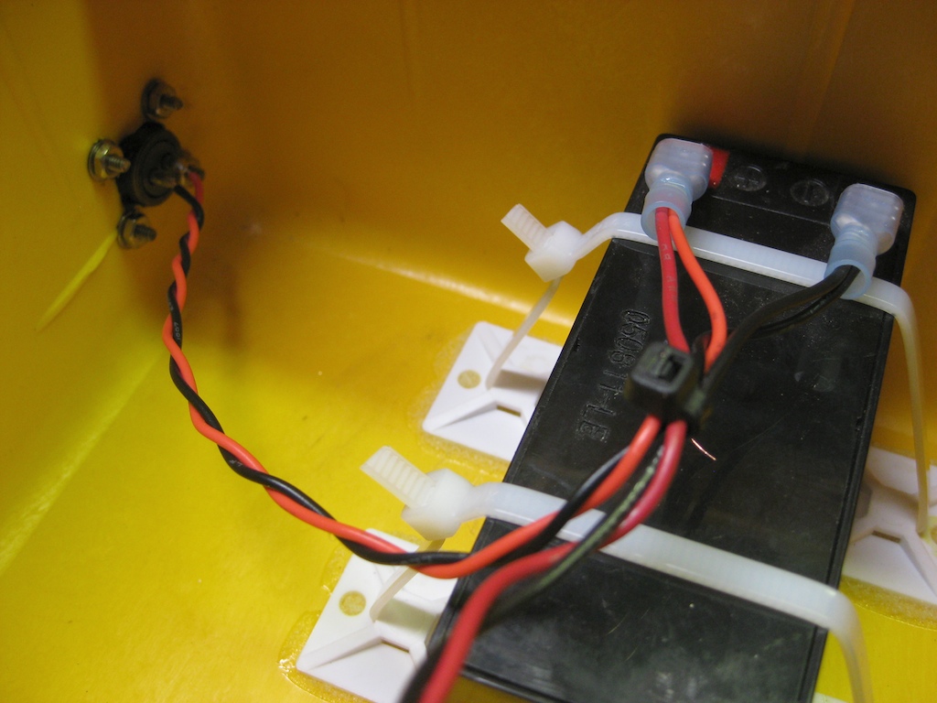
images/wiring/battery_2.jpg
