vinmarshall/Radio-Shack-Time-Lapse/images/wiring/battery_3.jpg

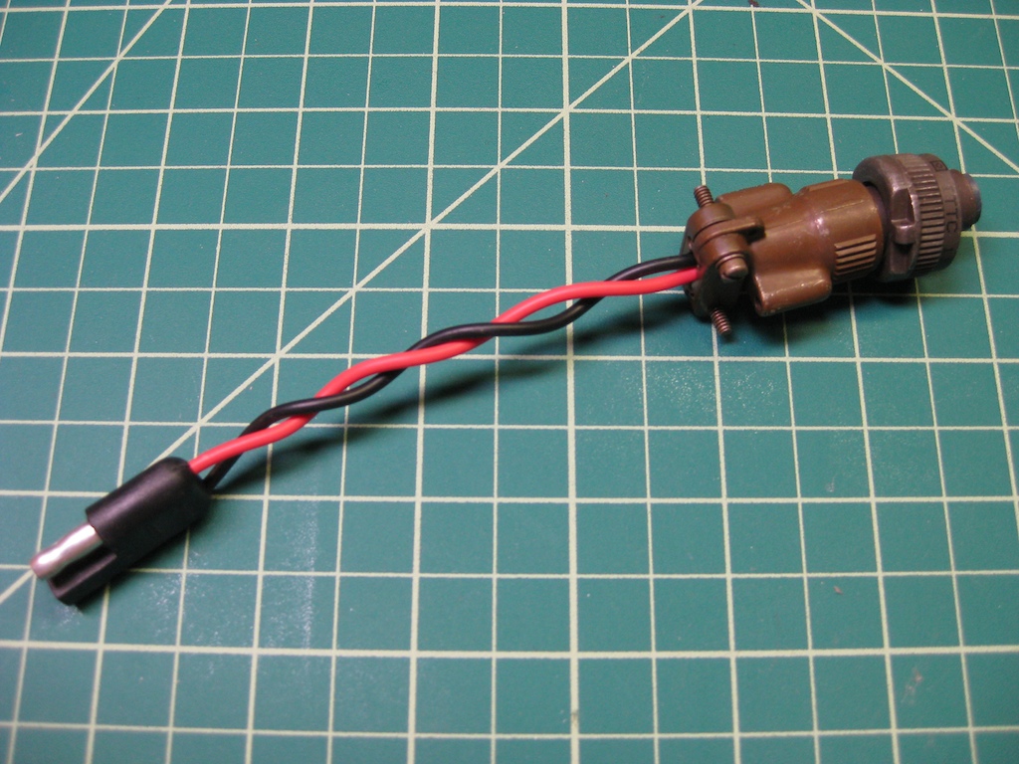
images/wiring/battery_3.jpg
