vinmarshall/Radio-Shack-Time-Lapse/images/wiring/camera_power.jpg

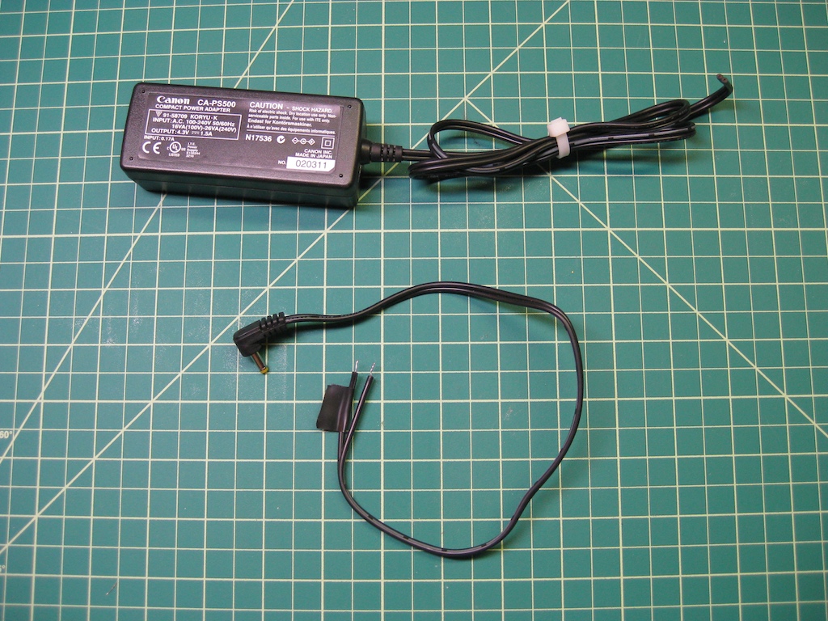
images/wiring/camera_power.jpg
