vinmarshall/Radio-Shack-Time-Lapse/images/wiring/daylight_sensor_2.jpg

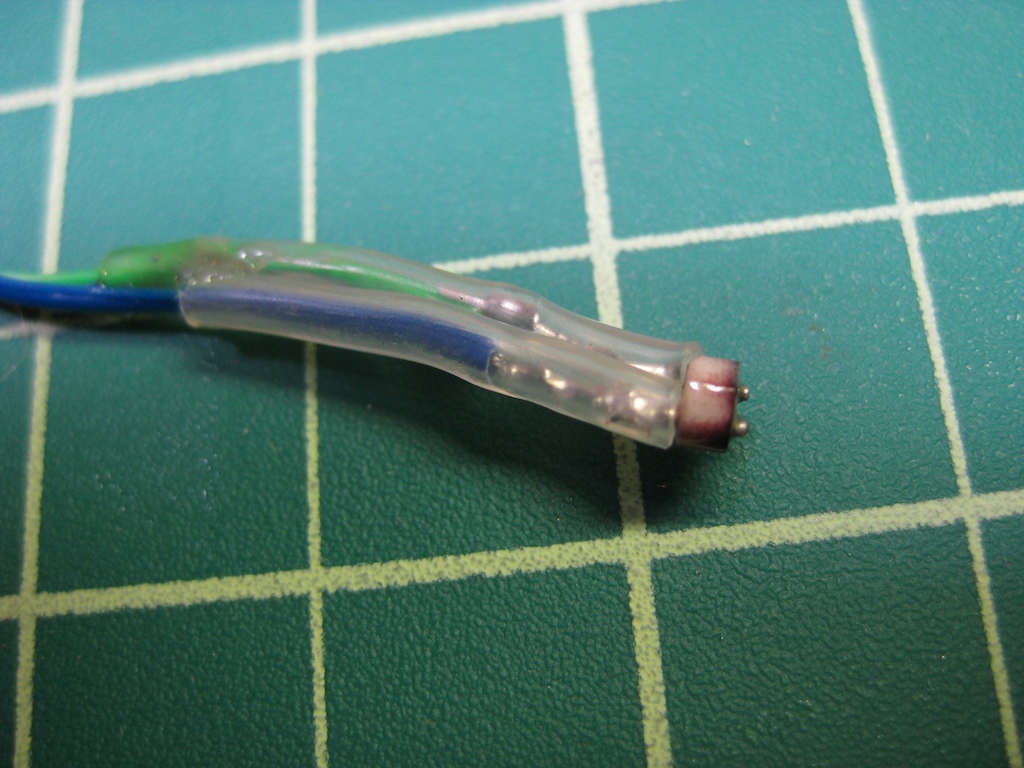
images/wiring/daylight_sensor_2.jpg
