vinmarshall/Radio-Shack-Time-Lapse/images/wiring/daylight_sensor_3.jpg

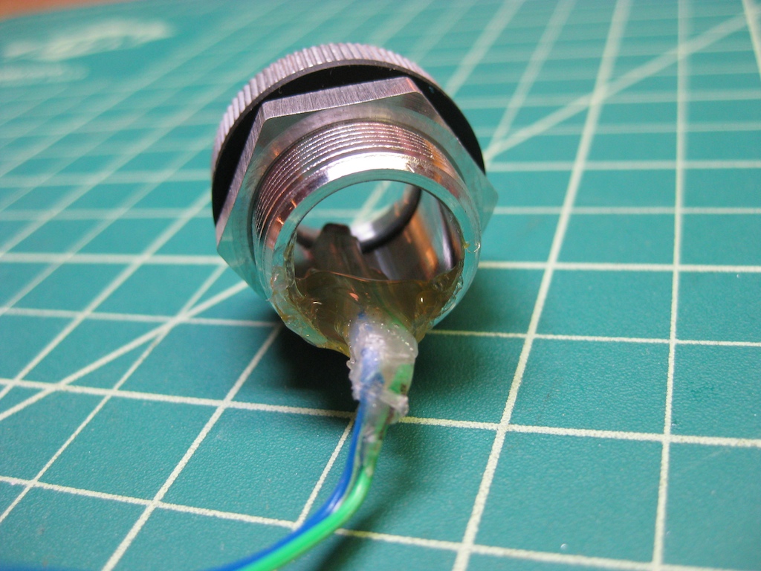
images/wiring/daylight_sensor_3.jpg
