vinmarshall/Radio-Shack-Time-Lapse/images/wiring/wiring_layout.jpg

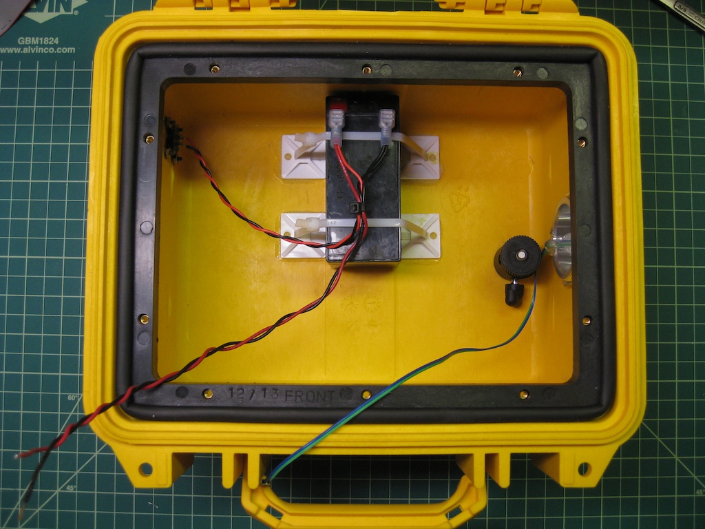
images/wiring/wiring_layout.jpg
